wickerwaka/Arcade-IremM92_MiSTer/docs/m92_A-B_B-F/audio.kicad_sch

## KiCad design docs/m92_A-B_B-F/audio.kicad_sch (2023-03-26)

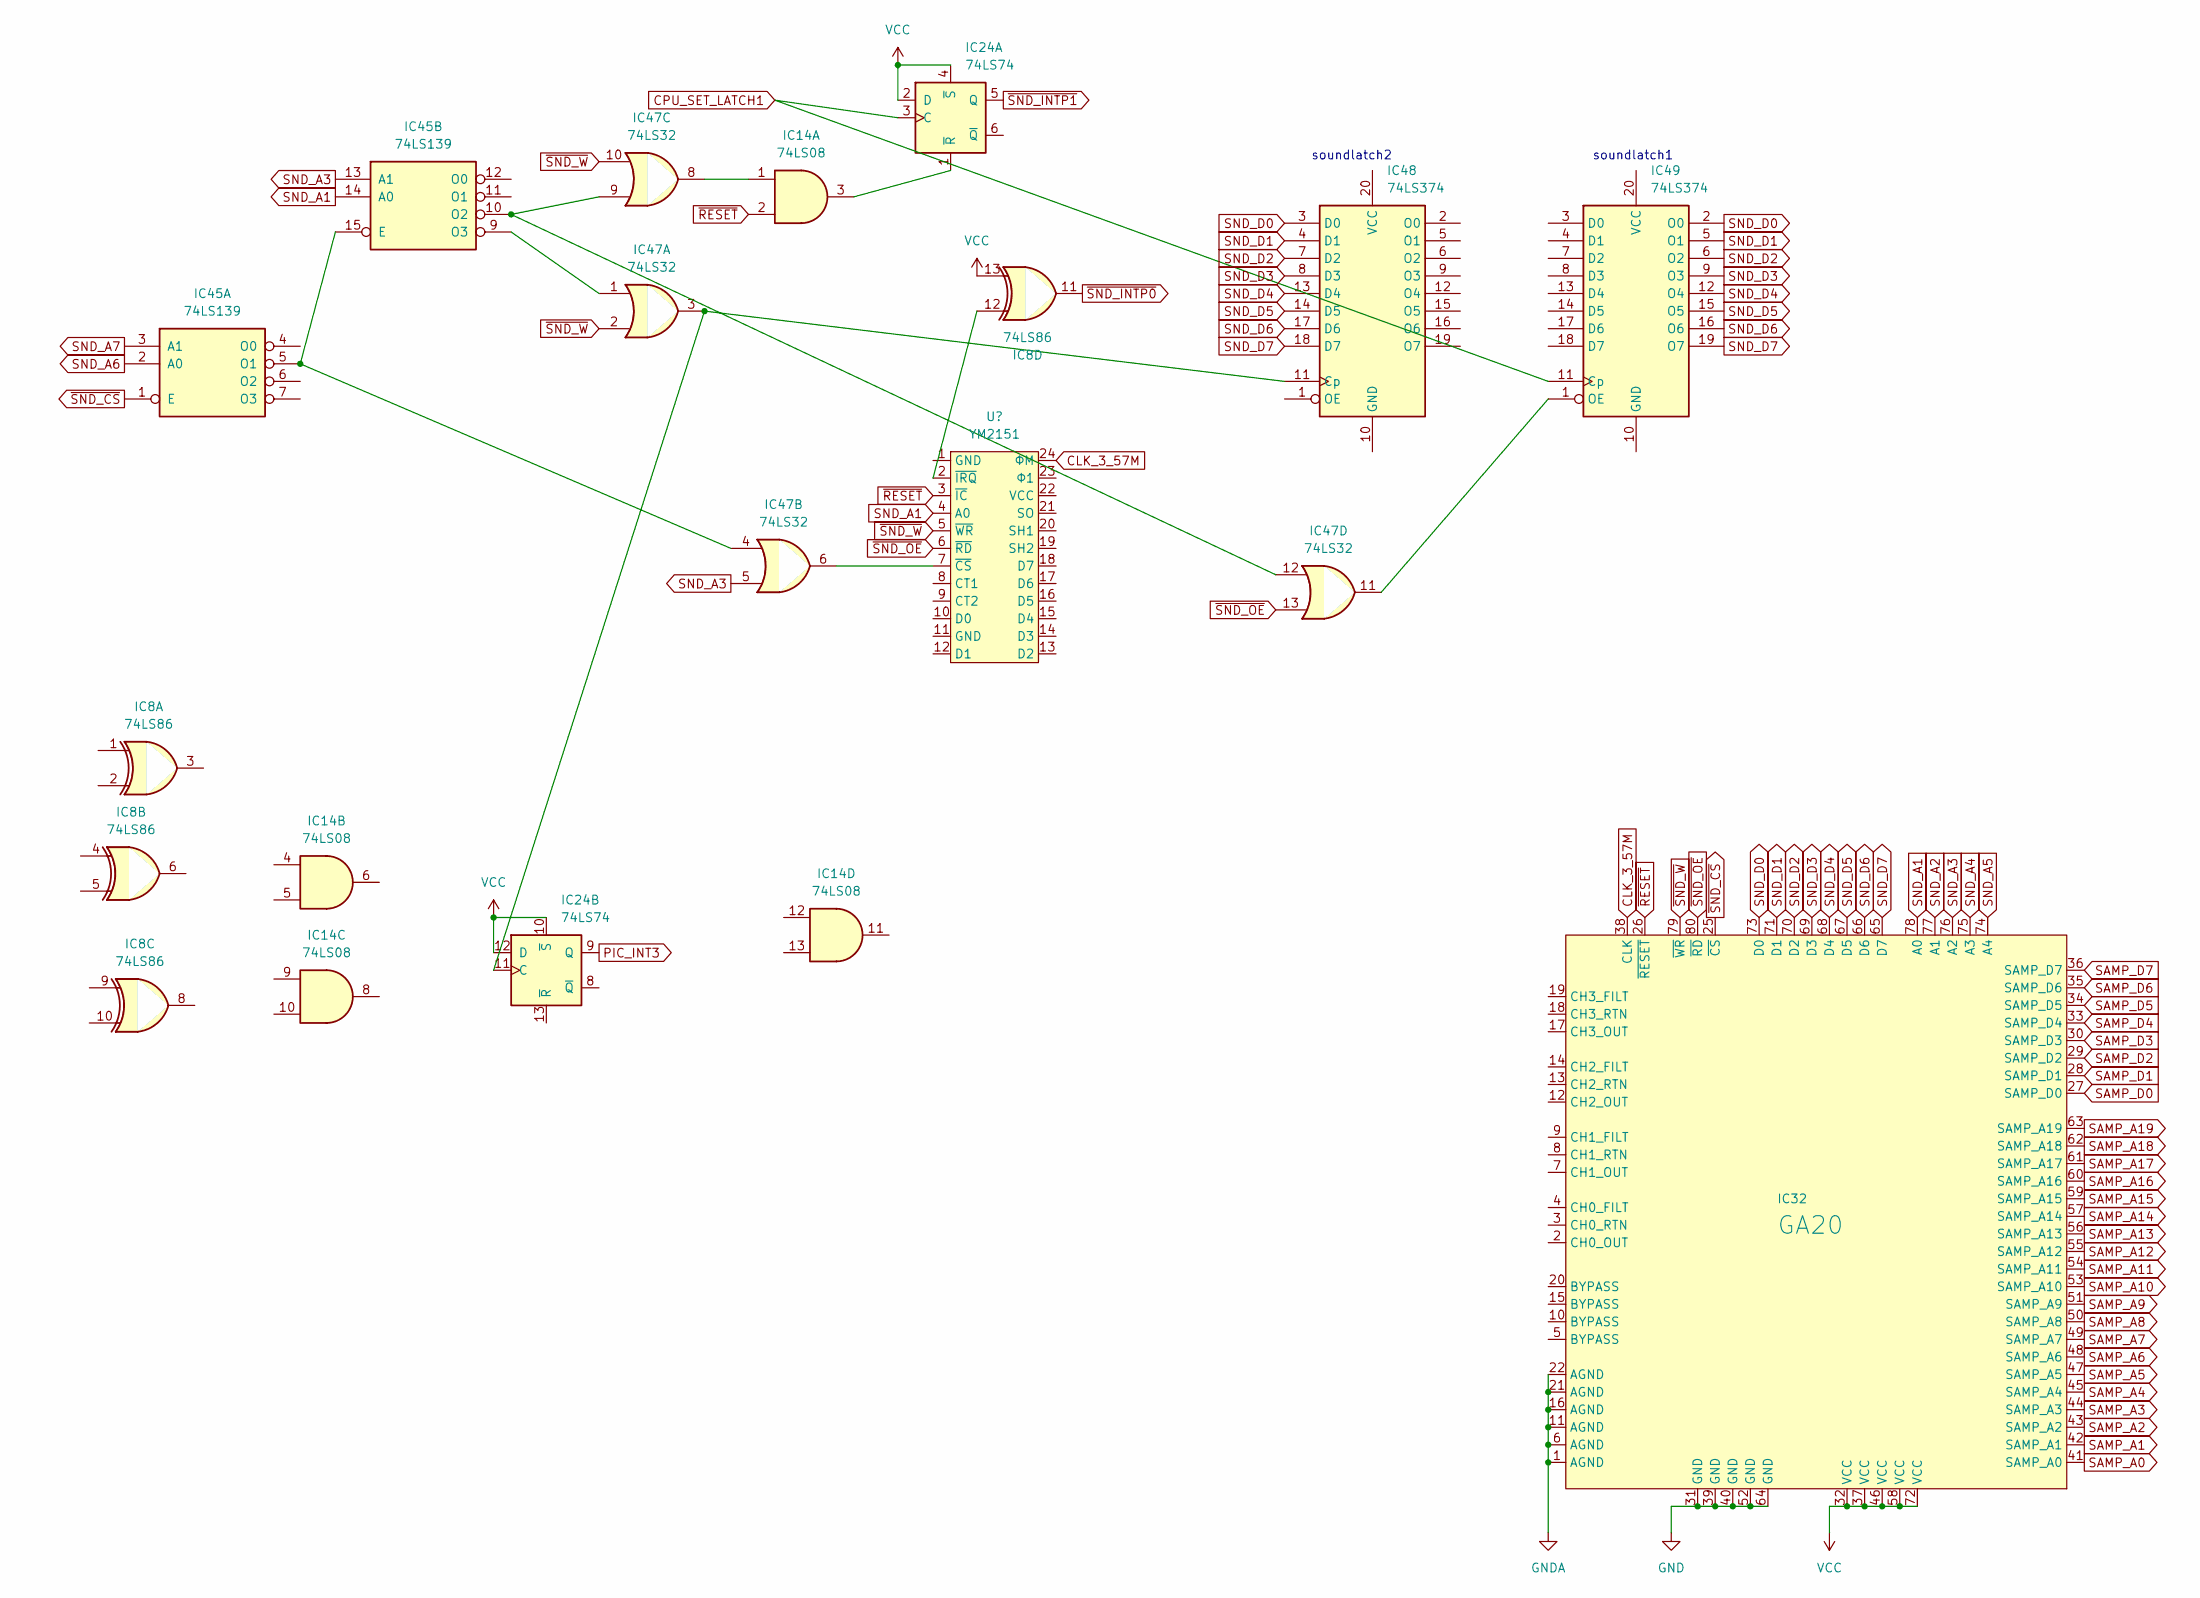
[picture p6: schematic audio.kicad_sch]

Parts:
IC8: 74LS86
IC14: 74LS08
IC24: 74LS74
IC32: GA20
IC45: 74LS139
IC47: 74LS32
IC48, IC49: 74LS374

Connections:
CLK_3_57M: IC32.38 (CLK)
CPU_SET_LATCH1: IC24.3 (C), IC49.11 (Cp)
unnamed: IC14.1, IC47.8
unnamed: IC14.3, IC24.1 (~R)
unnamed: IC24.2 (D), IC24.4 (~S)
unnamed: IC24.10 (~S), IC24.12 (D)
unnamed: IC24.11 (C), IC47.3, IC48.11 (Cp)
unnamed: IC32.1 (AGND), IC32.6 (AGND), IC32.11 (AGND), IC32.16 (AGND), IC32.21 (AGND), IC32.22 (AGND)
unnamed: IC32.31 (GND), IC32.39 (GND), IC32.40 (GND), IC32.52 (GND), IC32.64 (GND)
unnamed: IC32.32 (VCC), IC32.37 (VCC), IC32.46 (VCC), IC32.58 (VCC), IC32.72 (VCC)
unnamed: IC45.9 (O3), IC47.1
unnamed: IC45.10 (O2), IC47.9, IC47.12
unnamed: IC45.5 (O1), IC45.15 (E), IC47.4
unnamed: IC47.11, IC49.1 (OE)
PIC_INT3: IC24.9 (Q)
SAMP_A0: IC32.41 (SAMP_A0)
SAMP_A1: IC32.42 (SAMP_A1)
SAMP_A2: IC32.43 (SAMP_A2)
SAMP_A3: IC32.44 (SAMP_A3)
SAMP_A4: IC32.45 (SAMP_A4)
SAMP_A5: IC32.47 (SAMP_A5)
SAMP_A6: IC32.48 (SAMP_A6)
SAMP_A7: IC32.49 (SAMP_A7)
SAMP_A8: IC32.50 (SAMP_A8)
SAMP_A9: IC32.51 (SAMP_A9)
SAMP_A10: IC32.53 (SAMP_A10)
SAMP_A11: IC32.54 (SAMP_A11)
SAMP_A12: IC32.55 (SAMP_A12)
SAMP_A13: IC32.56 (SAMP_A13)
SAMP_A14: IC32.57 (SAMP_A14)
SAMP_A15: IC32.59 (SAMP_A15)
SAMP_A16: IC32.60 (SAMP_A16)
SAMP_A17: IC32.61 (SAMP_A17)
SAMP_A18: IC32.62 (SAMP_A18)
SAMP_A19: IC32.63 (SAMP_A19)
SAMP_D0: IC32.27 (SAMP_D0)
SAMP_D1: IC32.28 (SAMP_D1)
SAMP_D2: IC32.29 (SAMP_D2)
SAMP_D3: IC32.30 (SAMP_D3)
SAMP_D4: IC32.33 (SAMP_D4)
SAMP_D5: IC32.34 (SAMP_D5)
SAMP_D6: IC32.35 (SAMP_D6)
SAMP_D7: IC32.36 (SAMP_D7)
SND_A1: IC32.78 (A0), IC45.14 (A0)
SND_A2: IC32.77 (A1)
SND_A3: IC32.76 (A2), IC45.13 (A1), IC47.5
SND_A4: IC32.75 (A3)
SND_A5: IC32.74 (A4)
SND_A6: IC45.2 (A0)
SND_A7: IC45.3 (A1)
SND_D0: IC32.73 (D0), IC48.3 (D0), IC49.2 (O0)
SND_D1: IC32.71 (D1), IC48.4 (D1), IC49.5 (O1)
SND_D2: IC32.70 (D2), IC48.7 (D2), IC49.6 (O2)
SND_D3: IC32.69 (D3), IC48.8 (D3), IC49.9 (O3)
SND_D4: IC32.68 (D4), IC48.13 (D4), IC49.12 (O4)
SND_D5: IC32.67 (D5), IC48.14 (D5), IC49.15 (O5)
SND_D6: IC32.66 (D6), IC48.17 (D6), IC49.16 (O6)
SND_D7: IC32.65 (D7), IC48.18 (D7), IC49.19 (O7)
~RESET: IC14.2, IC32.26 (~RESET)
~SND_CS: IC32.25 (~CS), IC45.1 (E)
~SND_INTP0: IC8.11
~SND_INTP1: IC24.5 (Q)
~SND_OE: IC32.80 (~RD), IC47.13
~SND_W: IC32.79 (~WR), IC47.2, IC47.10

Notes on the sheet:
soundlatch2
soundlatch1
