wickerwaka/Arcade-IremM92_MiSTer/docs/m92_A-B_B-F/audio_cpu.kicad_sch

## KiCad design docs/m92_A-B_B-F/audio_cpu.kicad_sch (2023-03-26)

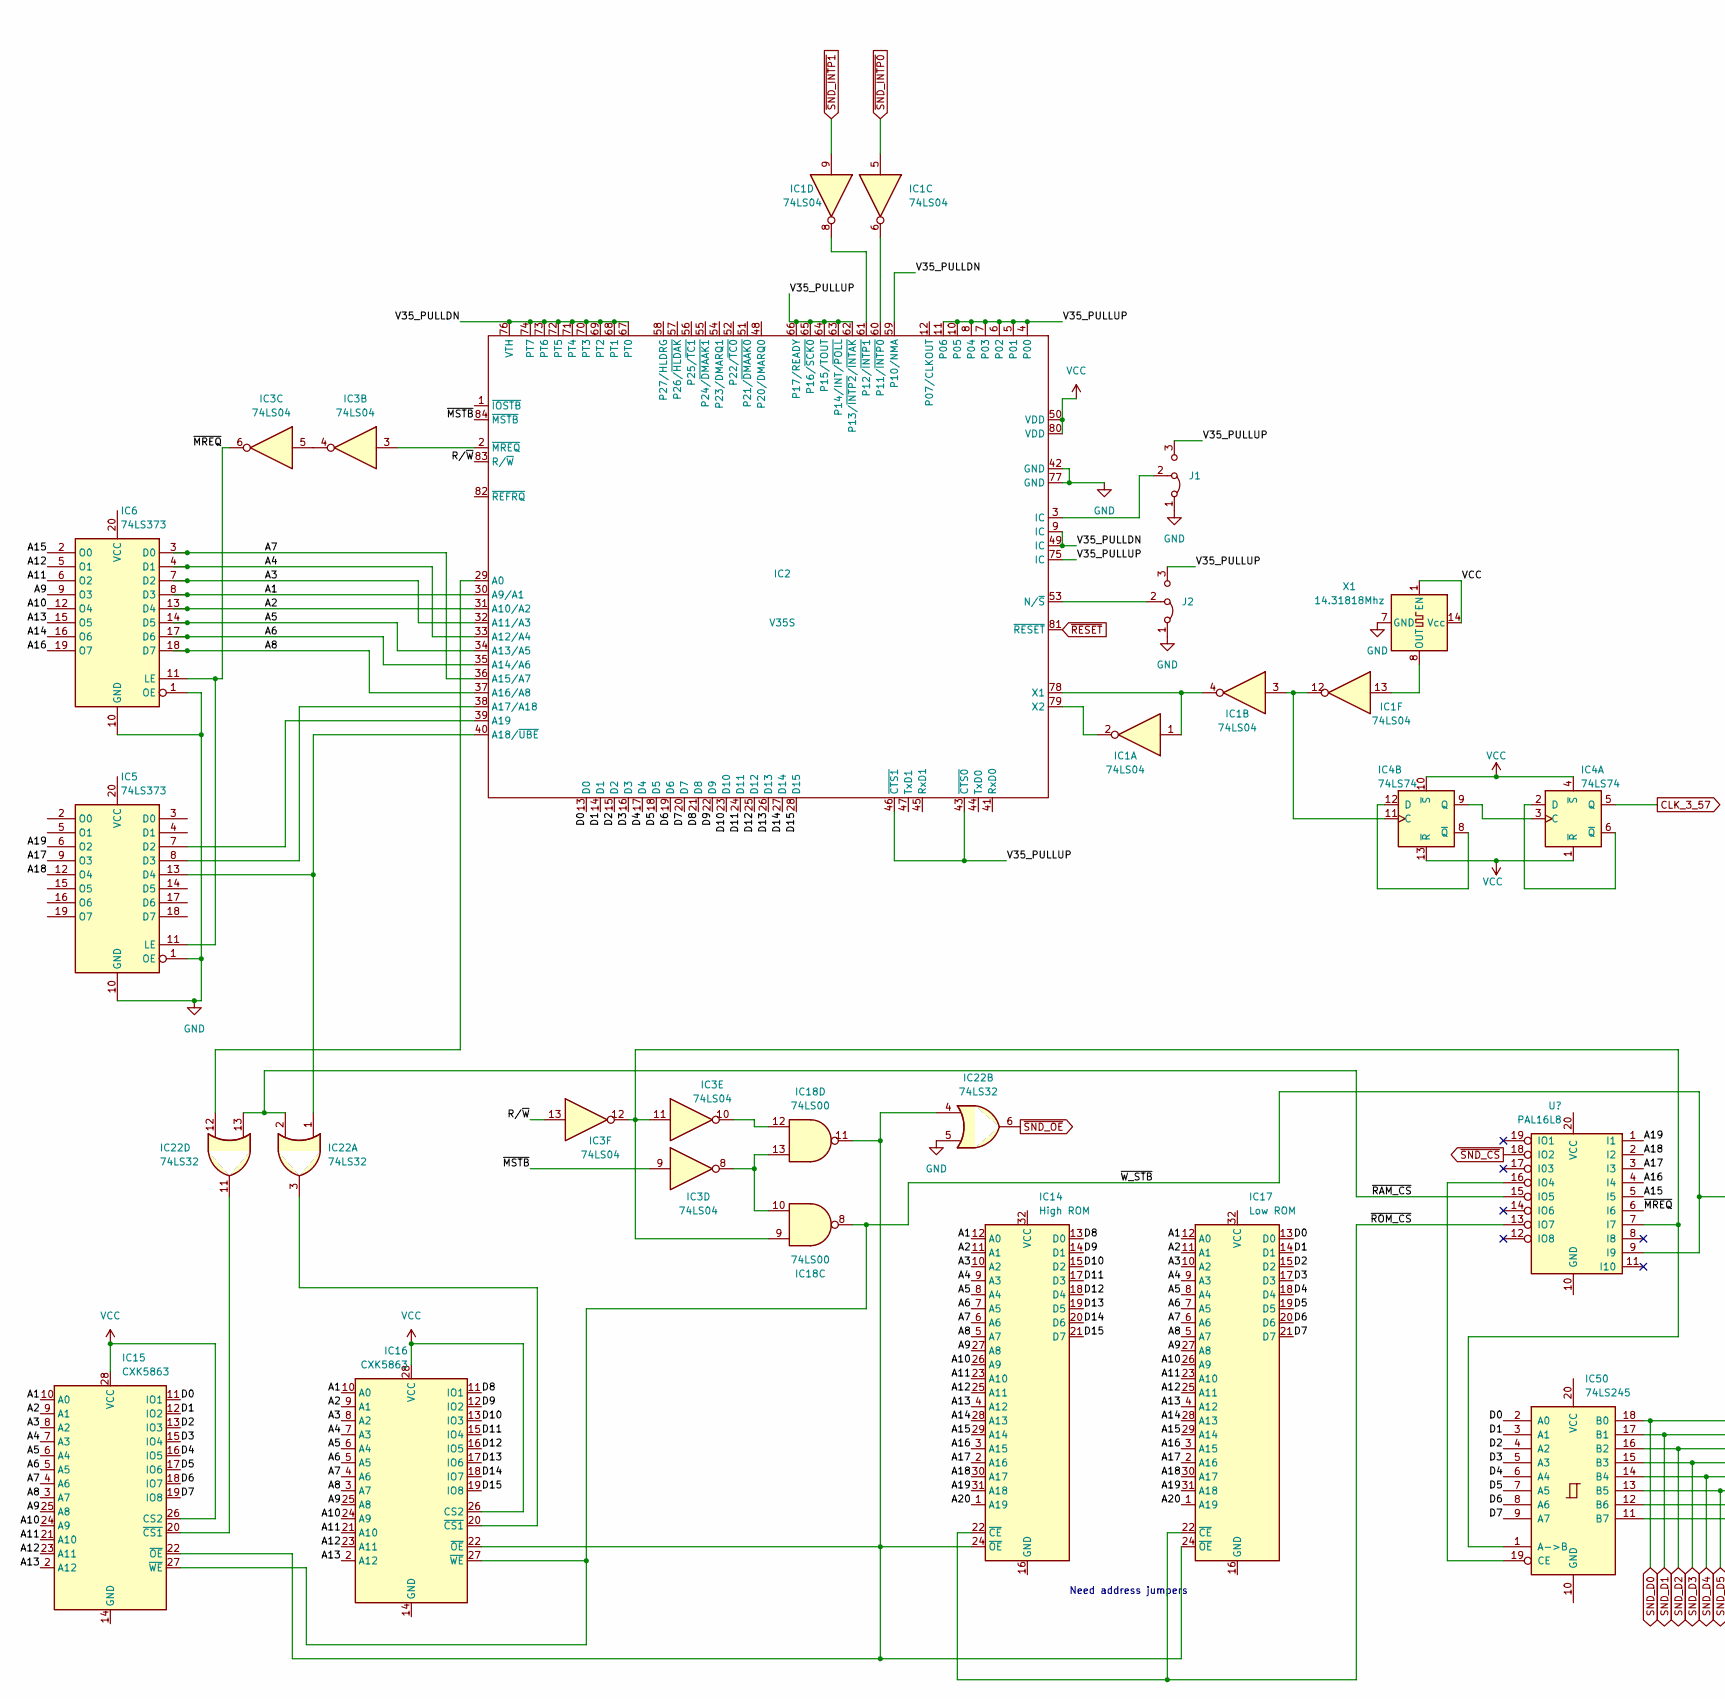
[picture p7: schematic audio_cpu.kicad_sch, part in row 1, column 1]

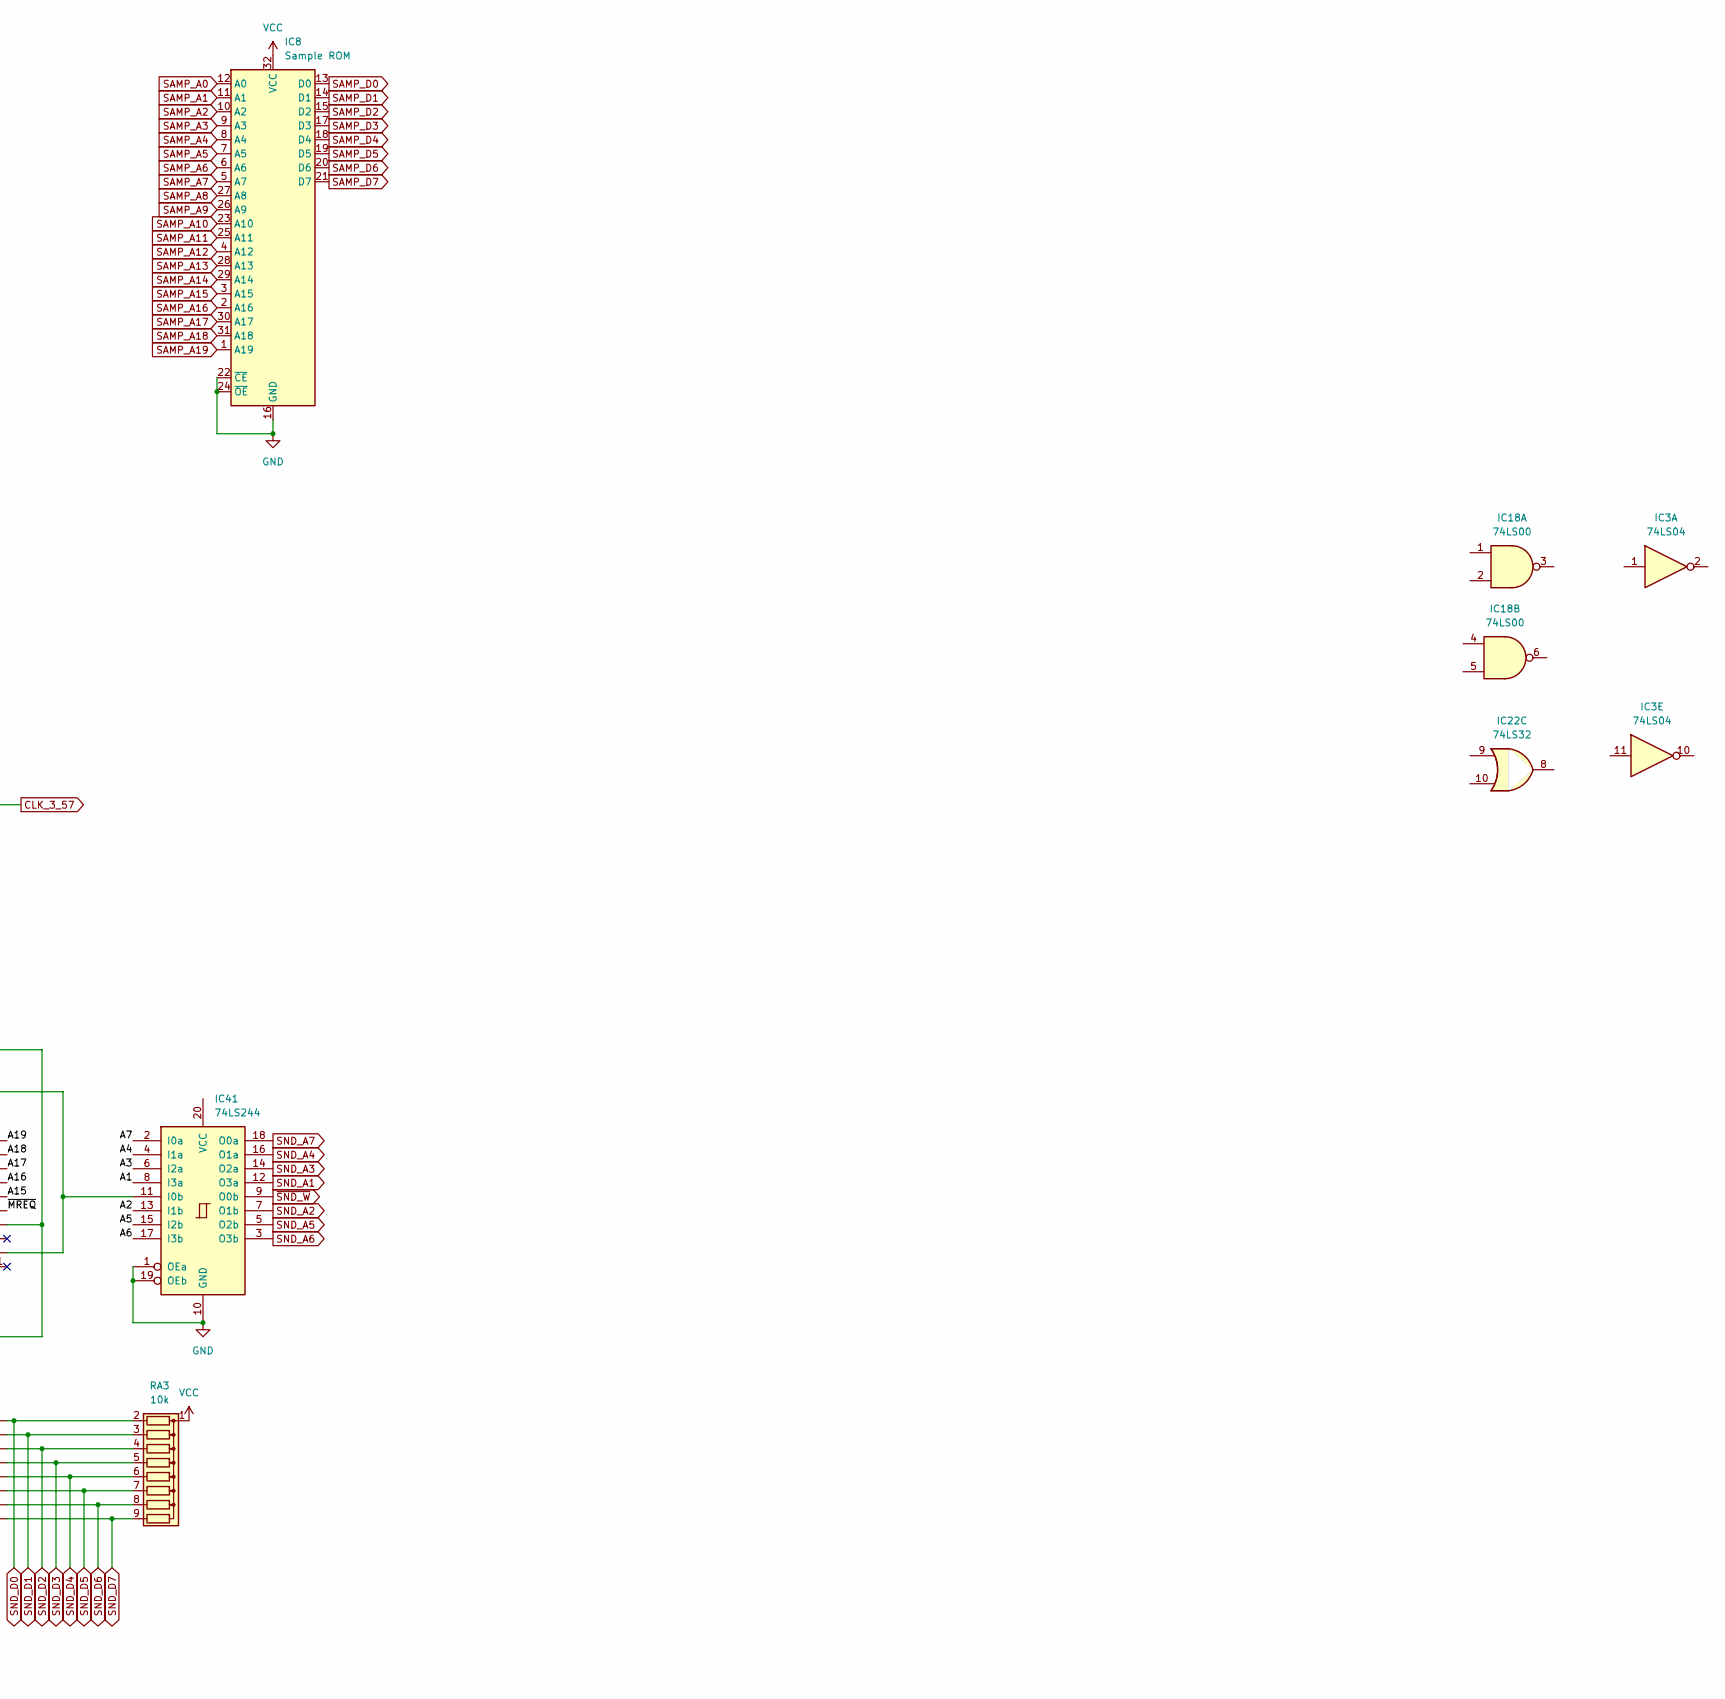
[picture p8: schematic audio_cpu.kicad_sch, part in row 1, column 2]

Parts:
IC1, IC3: 74LS04
IC2: V35S
IC4: 74LS74
IC5, IC6: 74LS373
IC8: Sample ROM
IC14: High ROM
IC15, IC16: CXK5863; DIP-28_W15.24mm
IC17: Low ROM
IC18: 74LS00
IC22: 74LS32
IC41: 74LS244
IC50: 74LS245
J1, J2: Jumper_3_Bridged12
RA3: 10k; R_Array_SIP9
X1: 14.31818Mhz; Oscillator_DIP-14

Connections:
A1: IC2.30 (A9/A1), IC6.8 (D3), IC14.12 (A0), IC15.10 (A0), IC16.10 (A0), IC17.12 (A0), IC41.8 (I3a)
A2: IC2.31 (A10/A2), IC6.13 (D4), IC14.11 (A1), IC15.9 (A1), IC16.9 (A1), IC17.11 (A1), IC41.13 (I1b)
A3: IC2.32 (A11/A3), IC6.7 (D2), IC14.10 (A2), IC15.8 (A2), IC16.8 (A2), IC17.10 (A2), IC41.6 (I2a)
A4: IC2.33 (A12/A4), IC6.4 (D1), IC14.9 (A3), IC15.7 (A3), IC16.7 (A3), IC17.9 (A3), IC41.4 (I1a)
A5: IC2.34 (A13/A5), IC6.14 (D5), IC14.8 (A4), IC15.6 (A4), IC16.6 (A4), IC17.8 (A4), IC41.15 (I2b)
A6: IC2.35 (A14/A6), IC6.17 (D6), IC14.7 (A5), IC15.5 (A5), IC16.5 (A5), IC17.7 (A5), IC41.17 (I3b)
A7: IC2.36 (A15/A7), IC6.3 (D0), IC14.6 (A6), IC15.4 (A6), IC16.4 (A6), IC17.6 (A6), IC41.2 (I0a)
A8: IC2.37 (A16/A8), IC6.18 (D7), IC14.5 (A7), IC15.3 (A7), IC16.3 (A7), IC17.5 (A7)
A9: IC6.9 (O3), IC14.27 (A8), IC15.25 (A8), IC16.25 (A8), IC17.27 (A8)
A10: IC6.12 (O4), IC14.26 (A9), IC15.24 (A9), IC16.24 (A9), IC17.26 (A9)
A11: IC6.6 (O2), IC14.23 (A10), IC15.21 (A10), IC16.21 (A10), IC17.23 (A10)
A12: IC6.5 (O1), IC14.25 (A11), IC15.23 (A11), IC16.23 (A11), IC17.25 (A11)
A13: IC6.15 (O5), IC14.4 (A12), IC15.2 (A12), IC16.2 (A12), IC17.4 (A12)
A14: IC6.16 (O6), IC14.28 (A13), IC17.28 (A13)
A15: IC6.2 (O0), IC14.29 (A14), IC17.29 (A14)
A16: IC6.19 (O7), IC14.3 (A15), IC17.3 (A15)
A17: IC5.9 (O3), IC14.2 (A16), IC17.2 (A16)
A18: IC5.12 (O4), IC14.30 (A17), IC17.30 (A17)
A19: IC5.6 (O2), IC14.31 (A18), IC17.31 (A18)
A20: IC14.1 (A19), IC17.1 (A19)
CLK_3_57: IC4.5 (Q)
D0: IC2.13 (D0), IC15.11 (IO1), IC17.13 (D0), IC50.2 (A0)
D1: IC2.14 (D1), IC15.12 (IO2), IC17.14 (D1), IC50.3 (A1)
D2: IC2.15 (D2), IC15.13 (IO3), IC17.15 (D2), IC50.4 (A2)
D3: IC2.16 (D3), IC15.15 (IO4), IC17.17 (D3), IC50.5 (A3)
D4: IC2.17 (D4), IC15.16 (IO5), IC17.18 (D4), IC50.6 (A4)
D5: IC2.18 (D5), IC15.17 (IO6), IC17.19 (D5), IC50.7 (A5)
D6: IC2.19 (D6), IC15.18 (IO7), IC17.20 (D6), IC50.8 (A6)
D7: IC2.20 (D7), IC15.19 (IO8), IC17.21 (D7), IC50.9 (A7)
D8: IC2.21 (D8), IC14.13 (D0), IC16.11 (IO1)
D9: IC2.22 (D9), IC14.14 (D1), IC16.12 (IO2)
D10: IC2.23 (D10), IC14.15 (D2), IC16.13 (IO3)
D11: IC2.24 (D11), IC14.17 (D3), IC16.15 (IO4)
D12: IC2.25 (D12), IC14.18 (D4), IC16.16 (IO5)
D13: IC2.26 (D13), IC14.19 (D5), IC16.17 (IO6)
D14: IC2.27 (D14), IC14.20 (D6), IC16.18 (IO7)
D15: IC2.28 (D15), IC14.21 (D7), IC16.19 (IO8)
unnamed: IC1.1, IC1.4, IC2.78 (X1)
unnamed: IC1.2, IC2.79 (X2)
unnamed: IC1.6, IC2.60 (P11/~INTP0)
unnamed: IC1.8, IC2.61 (P12/~INTP1)
unnamed: IC1.3, IC1.12, IC4.11 (C)
unnamed: IC1.13, X1.8 (OUT)
unnamed: IC2.2 (~MREQ), IC3.3
unnamed: IC2.3 (IC), J1.2 (C)
unnamed: IC2.29 (A0), IC22.12
unnamed: IC2.38 (A17/A18), IC5.8 (D3)
unnamed: IC2.39 (A19), IC5.7 (D2)
unnamed: IC2.40 (A18/~UBE), IC5.13 (D4), IC22.1
unnamed: IC2.42 (GND), IC2.77 (GND)
unnamed: IC2.50 (VDD), IC2.80 (VDD)
unnamed: IC2.53 (N/~S), J2.2 (C)
unnamed: IC3.4, IC3.5
unnamed: IC4.1 (~R), IC4.13 (~R)
unnamed: IC4.2 (D), IC4.6 (~Q)
unnamed: IC4.3 (C), IC4.9 (Q)
unnamed: IC4.4 (~S), IC4.10 (~S)
unnamed: IC4.8 (~Q), IC4.12 (D)
unnamed: IC5.1 (OE), IC5.10 (GND), IC6.1 (OE), IC6.10 (GND)
unnamed: IC8.16 (GND), IC8.22 (~CE), IC8.24 (~OE)
unnamed: IC14.24 (~OE), IC15.22 (~OE), IC16.22 (~OE), IC17.24 (~OE), IC18.11, IC22.4
unnamed: IC15.20 (~CS1), IC22.11
unnamed: IC15.26 (CS2), IC15.28 (VCC)
unnamed: IC16.20 (~CS1), IC22.3
unnamed: IC16.26 (CS2), IC16.28 (VCC)
unnamed: IC3.11, IC3.12, IC18.9, IC50.1 (A->B)
unnamed: IC3.8, IC18.10, IC18.13
unnamed: IC3.10, IC18.12
unnamed: IC41.1 (OEa), IC41.10 (GND), IC41.19 (OEb)
R/~W: IC2.83 (R/~W), IC3.13
SAMP_A0: IC8.12 (A0)
SAMP_A1: IC8.11 (A1)
SAMP_A2: IC8.10 (A2)
SAMP_A3: IC8.9 (A3)
SAMP_A4: IC8.8 (A4)
SAMP_A5: IC8.7 (A5)
SAMP_A6: IC8.6 (A6)
SAMP_A7: IC8.5 (A7)
SAMP_A8: IC8.27 (A8)
SAMP_A9: IC8.26 (A9)
SAMP_A10: IC8.23 (A10)
SAMP_A11: IC8.25 (A11)
SAMP_A12: IC8.4 (A12)
SAMP_A13: IC8.28 (A13)
SAMP_A14: IC8.29 (A14)
SAMP_A15: IC8.3 (A15)
SAMP_A16: IC8.2 (A16)
SAMP_A17: IC8.30 (A17)
SAMP_A18: IC8.31 (A18)
SAMP_A19: IC8.1 (A19)
SAMP_D0: IC8.13 (D0)
SAMP_D1: IC8.14 (D1)
SAMP_D2: IC8.15 (D2)
SAMP_D3: IC8.17 (D3)
SAMP_D4: IC8.18 (D4)
SAMP_D5: IC8.19 (D5)
SAMP_D6: IC8.20 (D6)
SAMP_D7: IC8.21 (D7)
SND_A1: IC41.12 (O3a)
SND_A2: IC41.7 (O1b)
SND_A3: IC41.14 (O2a)
SND_A4: IC41.16 (O1a)
SND_A5: IC41.5 (O2b)
SND_A6: IC41.3 (O3b)
SND_A7: IC41.18 (O0a)
SND_D0: IC50.18 (B0), RA3.2 (R1)
SND_D1: IC50.17 (B1), RA3.3 (R2)
SND_D2: IC50.16 (B2), RA3.4 (R3)
SND_D3: IC50.15 (B3), RA3.5 (R4)
SND_D4: IC50.14 (B4), RA3.6 (R5)
SND_D5: IC50.13 (B5), RA3.7 (R6)
SND_D6: IC50.12 (B6), RA3.8 (R7)
SND_D7: IC50.11 (B7), RA3.9 (R8)
V35_PULLDN: IC2.9 (IC), IC2.49 (IC), IC2.59 (P10/NMA), IC2.67 (PT0), IC2.68 (PT1), IC2.69 (PT2), IC2.70 (PT3), IC2.71 (PT4), IC2.72 (PT5), IC2.73 (PT6), IC2.74 (PT7), IC2.76 (VTH)
V35_PULLUP: IC2.4 (P00), IC2.5 (P01), IC2.6 (P02), IC2.7 (P03), IC2.8 (P04), IC2.10 (P05), IC2.11 (P06), IC2.43 (~CTS0), IC2.46 (~CTS1), IC2.62 (P13/~INTP2/~INTAK), IC2.63 (P14/INT/~POLL), IC2.64 (P15/TOUT), IC2.65 (P16/~SCK0), IC2.66 (P17/READY), IC2.75 (IC), J1.3 (B), J2.3 (B)
VCC: X1.1 (EN), X1.14 (Vcc)
~MREQ: IC3.6, IC5.11 (LE), IC6.11 (LE)
~MSTB: IC2.84 (~MSTB), IC3.9
~RAM_CS: IC22.2, IC22.13
~RESET: IC2.81 (~RESET)
~ROM_CS: IC14.22 (~CE), IC17.22 (~CE)
~SND_INTP0: IC1.5
~SND_INTP1: IC1.9
~SND_OE: IC22.6
~SND_W: IC41.9 (O0b)
~W_STB: IC15.27 (~WE), IC16.27 (~WE), IC18.8, IC41.11 (I0b)

Notes on the sheet:
Need address jumpers
