wickerwaka/Arcade-IremM92_MiSTer/docs/m92_A-B_B-F/audio_mix.kicad_sch

## KiCad design docs/m92_A-B_B-F/audio_mix.kicad_sch (2023-03-26)

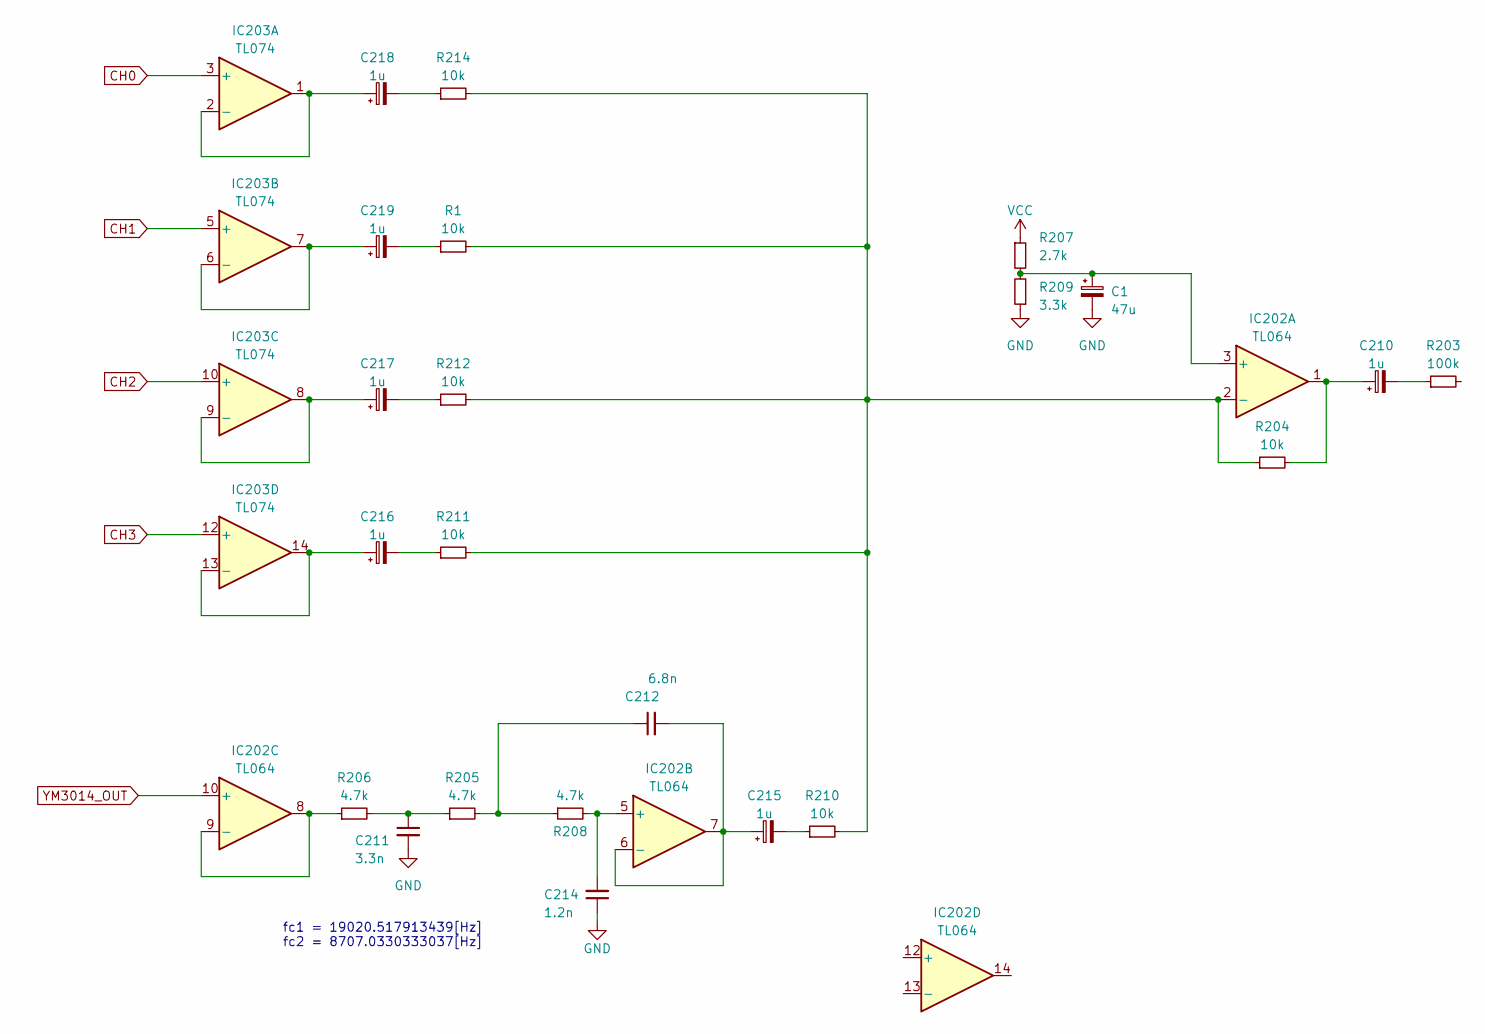
[picture p9: schematic audio_mix.kicad_sch]

Parts:
C1: 47u
C210, C215, C216, C217, C218, C219: 1u
C211: 3.3n
C212: 6.8n
C214: 1.2n
IC202: TL064
IC203: TL074
R1, R204, R210, R211, R212, R214: 10k
R203: 100k
R205, R206, R208: 4.7k
R207: 2.7k
R209: 3.3k

Connections:
CH0: IC203.3 (+)
CH1: IC203.5 (+)
CH2: IC203.10 (+)
CH3: IC203.12 (+)
GND: C1.2, C211.2, C214.1, R209.1
unnamed: C1.1, IC202.3 (+), R207.2, R209.2
unnamed: C210.1, IC202.1, R204.2
unnamed: C210.2, R203.1
unnamed: C211.1, R205.1, R206.2
unnamed: C212.1, R205.2, R208.1
unnamed: C212.2, C215.1, IC202.6 (-), IC202.7
unnamed: C214.2, IC202.5 (+), R208.2
unnamed: C215.2, R210.1
unnamed: C216.1, IC203.13 (-), IC203.14
unnamed: C216.2, R211.1
unnamed: C217.1, IC203.8, IC203.9 (-)
unnamed: C217.2, R212.1
unnamed: C218.1, IC203.1, IC203.2 (-)
unnamed: C218.2, R214.1
unnamed: C219.1, IC203.6 (-), IC203.7
unnamed: C219.2, R1.1
unnamed: IC202.2 (-), R1.2, R204.1, R210.2, R211.2, R212.2, R214.2
unnamed: IC202.8, IC202.9 (-), R206.1
VCC: R207.1
YM3014_OUT: IC202.10 (+)

Notes on the sheet:
fc1 = 19020.517913439[Hz] fc2 = 8707.0330333037[Hz]
