wickerwaka/Arcade-IremM92_MiSTer/docs/m92_A-B_B-F/b_board_support.kicad_sch

## KiCad design docs/m92_A-B_B-F/b_board_support.kicad_sch (2023-03-26)

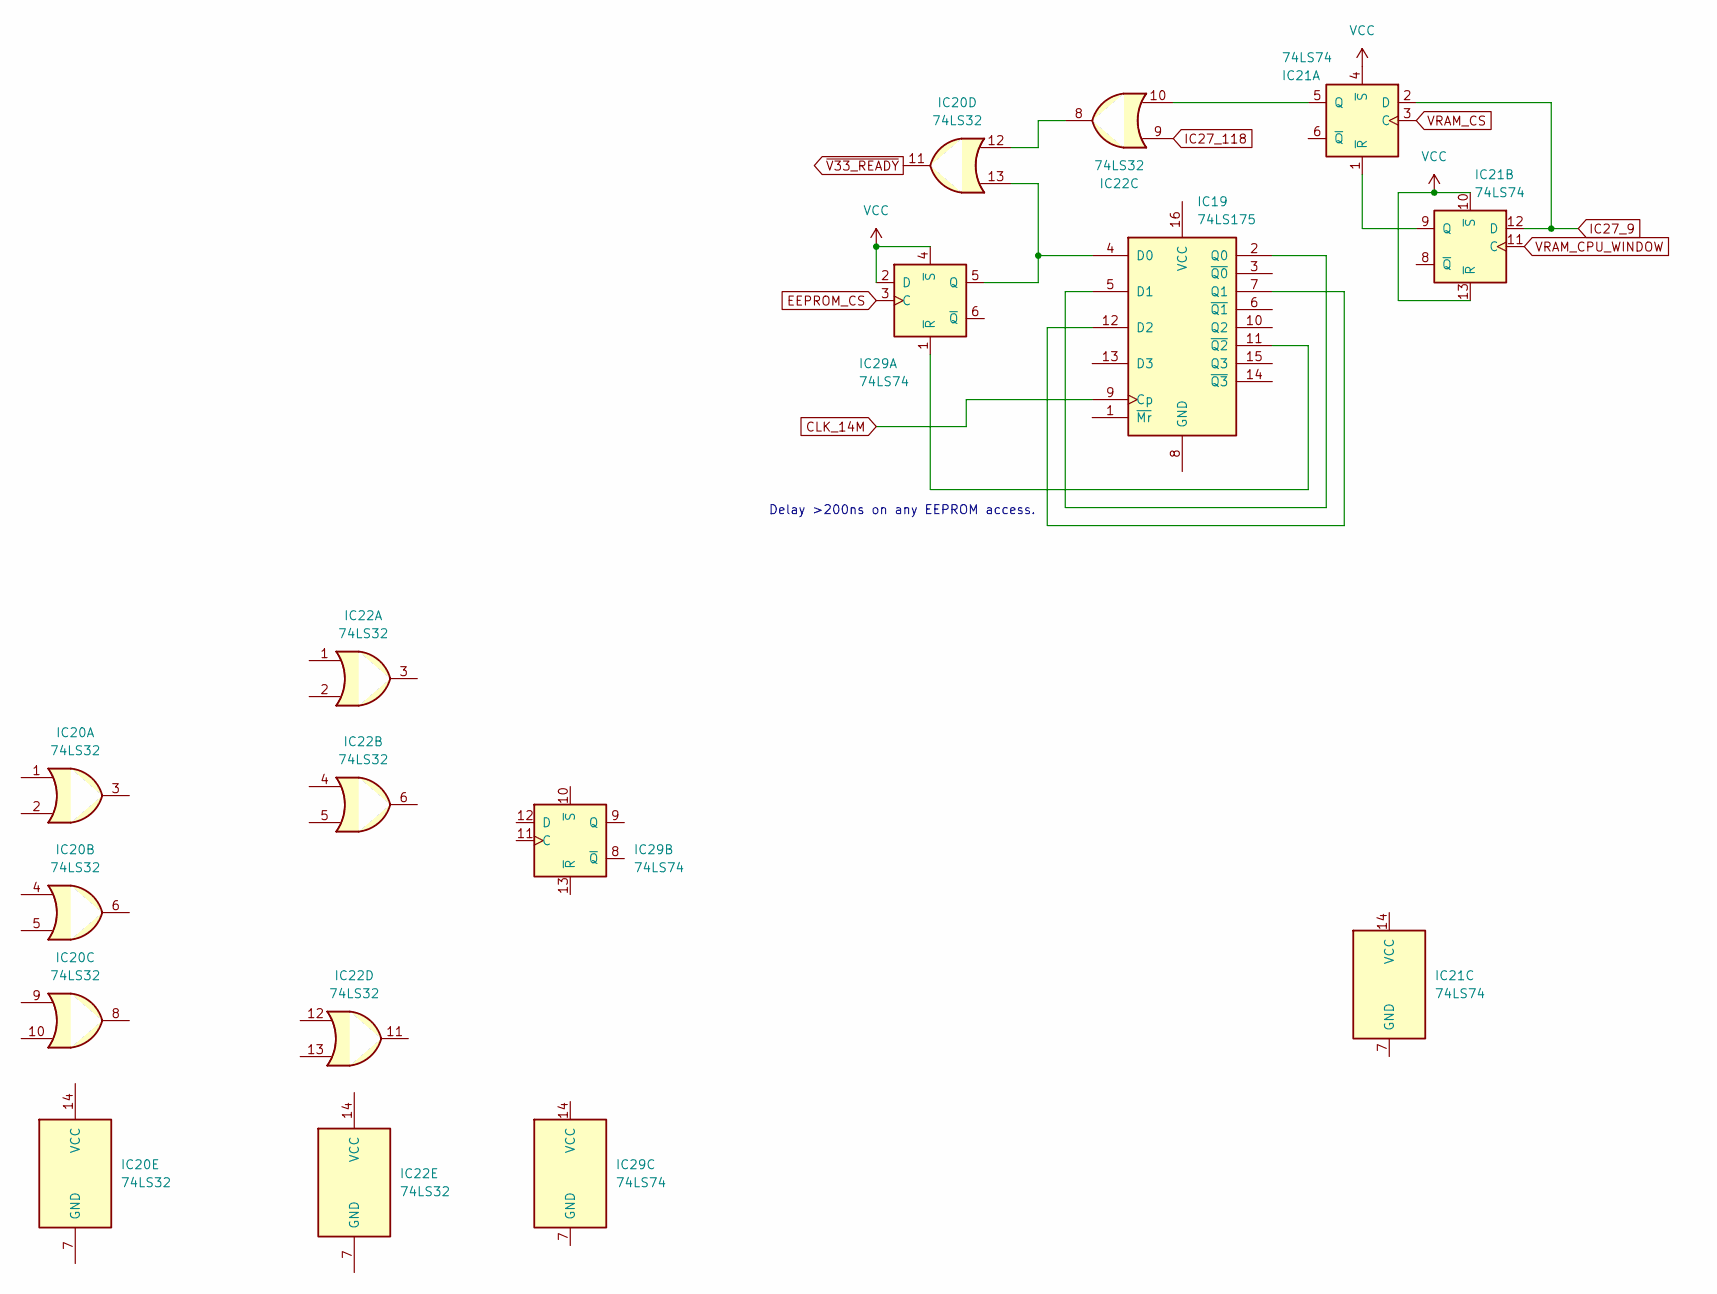
[picture p10: schematic b_board_support.kicad_sch]

Parts:
IC19: 74LS175
IC20, IC22: 74LS32
IC21, IC29: 74LS74

Connections:
CLK_14M: IC19.9 (Cp)
EEPROM_CS: IC29.3 (C)
IC27_9: IC21.2 (D), IC21.12 (D)
IC27_118: IC22.9
unnamed: IC19.2 (Q0), IC19.5 (D1)
unnamed: IC19.4 (D0), IC20.13, IC29.5 (Q)
unnamed: IC19.11 (~Q2), IC29.1 (~R)
unnamed: IC19.7 (Q1), IC19.12 (D2)
unnamed: IC20.12, IC22.8
unnamed: IC21.1 (~R), IC21.9 (Q)
unnamed: IC21.5 (Q), IC22.10
unnamed: IC21.10 (~S), IC21.13 (~R)
unnamed: IC29.2 (D), IC29.4 (~S)
VRAM_CPU_WINDOW: IC21.11 (C)
VRAM_CS: IC21.3 (C)
~V33_READY: IC20.11

Notes on the sheet:
Delay >200ns on any EEPROM access.
