wickerwaka/Arcade-IremM92_MiSTer/docs/m92_A-B_B-F/b_interface.kicad_sch

## KiCad design docs/m92_A-B_B-F/b_interface.kicad_sch (2023-03-26)

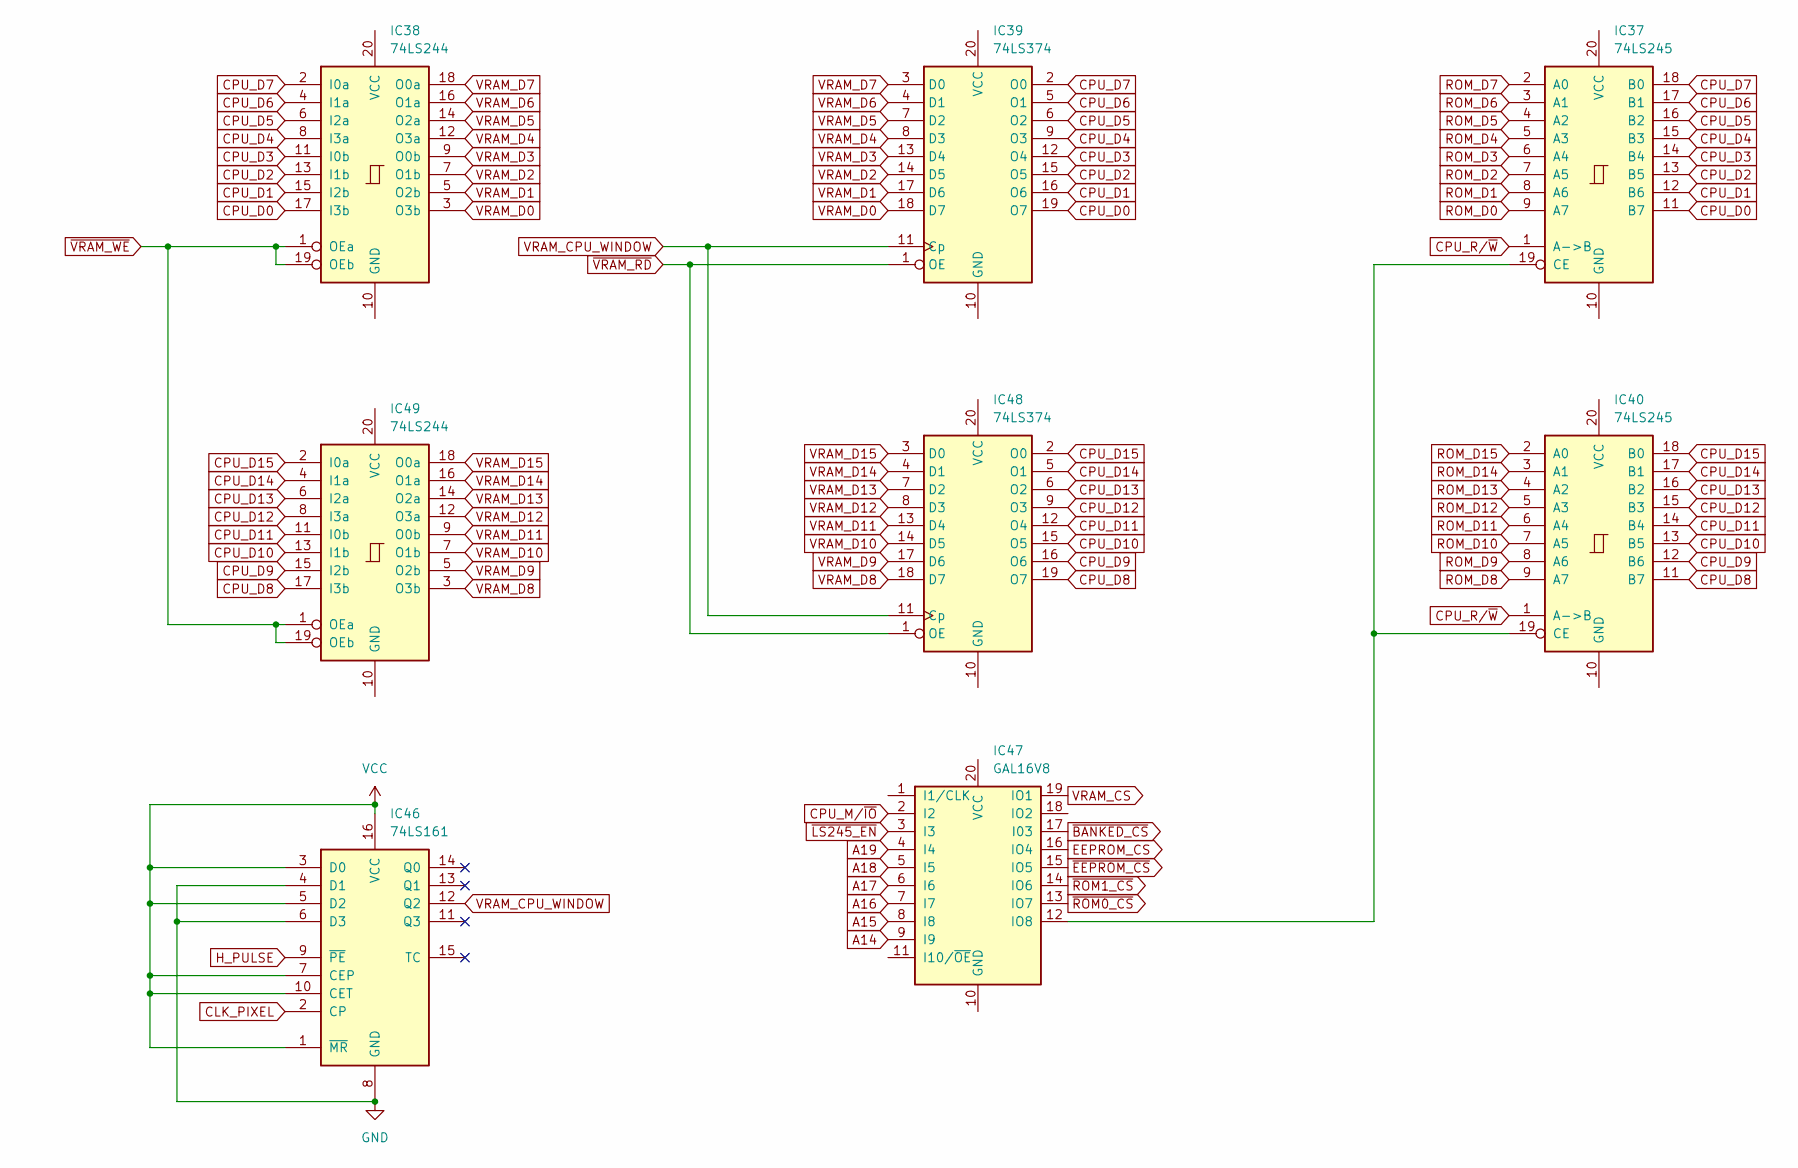
[picture p11: schematic b_interface.kicad_sch]

Parts:
IC37, IC40: 74LS245
IC38, IC49: 74LS244
IC39, IC48: 74LS374
IC46: 74LS161
IC47: GAL16V8

Connections:
A14: IC47.9 (I9)
A15: IC47.8 (I8)
A16: IC47.7 (I7)
A17: IC47.6 (I6)
A18: IC47.5 (I5)
A19: IC47.4 (I4)
CLK_PIXEL: IC46.2 (CP)
CPU_D0: IC37.11 (B7), IC38.17 (I3b), IC39.19 (O7)
CPU_D1: IC37.12 (B6), IC38.15 (I2b), IC39.16 (O6)
CPU_D2: IC37.13 (B5), IC38.13 (I1b), IC39.15 (O5)
CPU_D3: IC37.14 (B4), IC38.11 (I0b), IC39.12 (O4)
CPU_D4: IC37.15 (B3), IC38.8 (I3a), IC39.9 (O3)
CPU_D5: IC37.16 (B2), IC38.6 (I2a), IC39.6 (O2)
CPU_D6: IC37.17 (B1), IC38.4 (I1a), IC39.5 (O1)
CPU_D7: IC37.18 (B0), IC38.2 (I0a), IC39.2 (O0)
CPU_D8: IC40.11 (B7), IC48.19 (O7), IC49.17 (I3b)
CPU_D9: IC40.12 (B6), IC48.16 (O6), IC49.15 (I2b)
CPU_D10: IC40.13 (B5), IC48.15 (O5), IC49.13 (I1b)
CPU_D11: IC40.14 (B4), IC48.12 (O4), IC49.11 (I0b)
CPU_D12: IC40.15 (B3), IC48.9 (O3), IC49.8 (I3a)
CPU_D13: IC40.16 (B2), IC48.6 (O2), IC49.6 (I2a)
CPU_D14: IC40.17 (B1), IC48.5 (O1), IC49.4 (I1a)
CPU_D15: IC40.18 (B0), IC48.2 (O0), IC49.2 (I0a)
CPU_M/~IO: IC47.2 (I2)
CPU_R/~W: IC37.1 (A->B), IC40.1 (A->B)
EEPROM_CS: IC47.16 (IO4)
H_PULSE: IC46.9 (~PE)
unnamed: IC37.19 (CE), IC40.19 (CE), IC47.12 (IO8)
unnamed: IC46.1 (~MR), IC46.3 (D0), IC46.5 (D2), IC46.7 (CEP), IC46.10 (CET), IC46.16 (VCC)
unnamed: IC46.4 (D1), IC46.6 (D3), IC46.8 (GND)
ROM_D0: IC37.9 (A7)
ROM_D1: IC37.8 (A6)
ROM_D2: IC37.7 (A5)
ROM_D3: IC37.6 (A4)
ROM_D4: IC37.5 (A3)
ROM_D5: IC37.4 (A2)
ROM_D6: IC37.3 (A1)
ROM_D7: IC37.2 (A0)
ROM_D8: IC40.9 (A7)
ROM_D9: IC40.8 (A6)
ROM_D10: IC40.7 (A5)
ROM_D11: IC40.6 (A4)
ROM_D12: IC40.5 (A3)
ROM_D13: IC40.4 (A2)
ROM_D14: IC40.3 (A1)
ROM_D15: IC40.2 (A0)
VRAM_CPU_WINDOW: IC39.11 (Cp), IC46.12 (Q2), IC48.11 (Cp)
VRAM_CS: IC47.19 (IO1)
VRAM_D0: IC38.3 (O3b), IC39.18 (D7)
VRAM_D1: IC38.5 (O2b), IC39.17 (D6)
VRAM_D2: IC38.7 (O1b), IC39.14 (D5)
VRAM_D3: IC38.9 (O0b), IC39.13 (D4)
VRAM_D4: IC38.12 (O3a), IC39.8 (D3)
VRAM_D5: IC38.14 (O2a), IC39.7 (D2)
VRAM_D6: IC38.16 (O1a), IC39.4 (D1)
VRAM_D7: IC38.18 (O0a), IC39.3 (D0)
VRAM_D8: IC48.18 (D7), IC49.3 (O3b)
VRAM_D9: IC48.17 (D6), IC49.5 (O2b)
VRAM_D10: IC48.14 (D5), IC49.7 (O1b)
VRAM_D11: IC48.13 (D4), IC49.9 (O0b)
VRAM_D12: IC48.8 (D3), IC49.12 (O3a)
VRAM_D13: IC48.7 (D2), IC49.14 (O2a)
VRAM_D14: IC48.4 (D1), IC49.16 (O1a)
VRAM_D15: IC48.3 (D0), IC49.18 (O0a)
~BANKED_CS: IC47.17 (I03)
~EEPROM_CS: IC47.15 (IO5)
~LS245_EN: IC47.3 (I3)
~ROM0_CS: IC47.13 (IO7)
~ROM1_CS: IC47.14 (IO6)
~VRAM_RD: IC39.1 (OE), IC48.1 (OE)
~VRAM_WE: IC38.1 (OEa), IC38.19 (OEb), IC49.1 (OEa), IC49.19 (OEb)
