wickerwaka/Arcade-IremM92_MiSTer/docs/m92_A-B_B-F/bank_switching.kicad_sch

## KiCad design docs/m92_A-B_B-F/bank_switching.kicad_sch (2023-03-26)

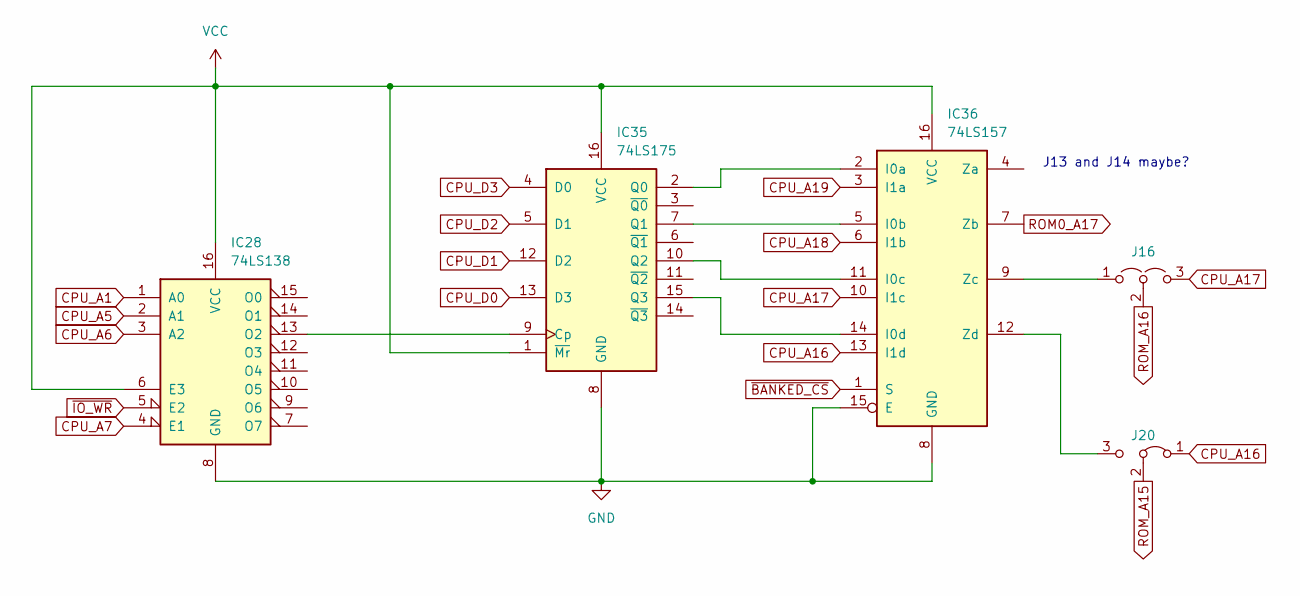
[picture p12: schematic bank_switching.kicad_sch]

Parts:
IC28: 74LS138
IC35: 74LS175
IC36: 74LS157
J16: Jumper_3_Open
J20: Jumper_3_Bridged12

Connections:
CPU_A1: IC28.1 (A0)
CPU_A5: IC28.2 (A1)
CPU_A6: IC28.3 (A2)
CPU_A7: IC28.4 (E1)
CPU_A16: IC36.13 (I1d), J20.1 (A)
CPU_A17: IC36.10 (I1c), J16.3 (B)
CPU_A18: IC36.6 (I1b)
CPU_A19: IC36.3 (I1a)
CPU_D0: IC35.13 (D3)
CPU_D1: IC35.12 (D2)
CPU_D2: IC35.5 (D1)
CPU_D3: IC35.4 (D0)
unnamed: IC28.8 (GND), IC35.8 (GND), IC36.8 (GND), IC36.15 (E)
unnamed: IC28.13 (O2), IC35.9 (Cp)
unnamed: IC28.6 (E3), IC28.16 (VCC), IC35.1 (~Mr), IC35.16 (VCC), IC36.16 (VCC)
unnamed: IC35.2 (Q0), IC36.2 (I0a)
unnamed: IC35.7 (Q1), IC36.5 (I0b)
unnamed: IC35.10 (Q2), IC36.11 (I0c)
unnamed: IC35.15 (Q3), IC36.14 (I0d)
unnamed: IC36.9 (Zc), J16.1 (A)
unnamed: IC36.12 (Zd), J20.3 (B)
ROM0_A17: IC36.7 (Zb)
ROM_A15: J20.2 (C)
ROM_A16: J16.2 (C)
~BANKED_CS: IC36.1 (S)
~IO_WR: IC28.5 (E2)

Notes on the sheet:
J13 and J14 maybe?
