wickerwaka/Arcade-IremM92_MiSTer/docs/m92_A-B_B-F/clock_gen.kicad_sch

## KiCad design docs/m92_A-B_B-F/clock_gen.kicad_sch (2023-03-26)

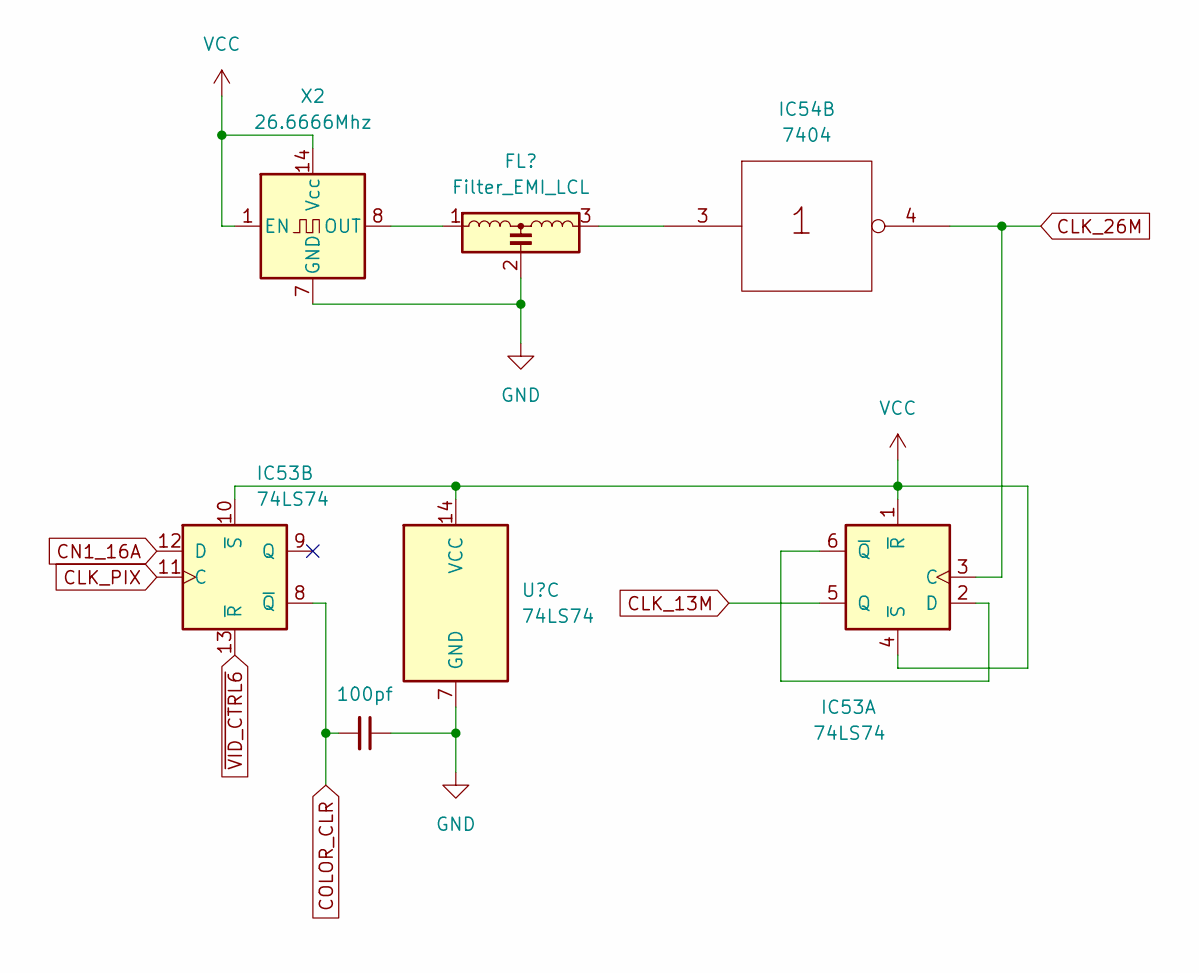
[picture p13: schematic clock_gen.kicad_sch]

Parts:
IC53: 74LS74
IC54: 7404
X2: 26.6666Mhz; Oscillator_DIP-14

Connections:
CLK_13M: IC53.5 (Q)
CLK_26M: IC53.3 (C), IC54.4
CLK_PIX: IC53.11 (C)
CN1_16A: IC53.12 (D)
COLOR_CLR: IC53.8 (~Q)
unnamed: IC53.1 (~R), IC53.4 (~S), IC53.10 (~S)
unnamed: IC53.2 (D), IC53.6 (~Q)
unnamed: X2.1 (EN), X2.14 (Vcc)
~VID_CTRL6: IC53.13 (~R)
