wickerwaka/Arcade-IremM92_MiSTer/docs/m92_A-B_B-F/connectors.kicad_sch

## KiCad design docs/m92_A-B_B-F/connectors.kicad_sch (2023-03-26)

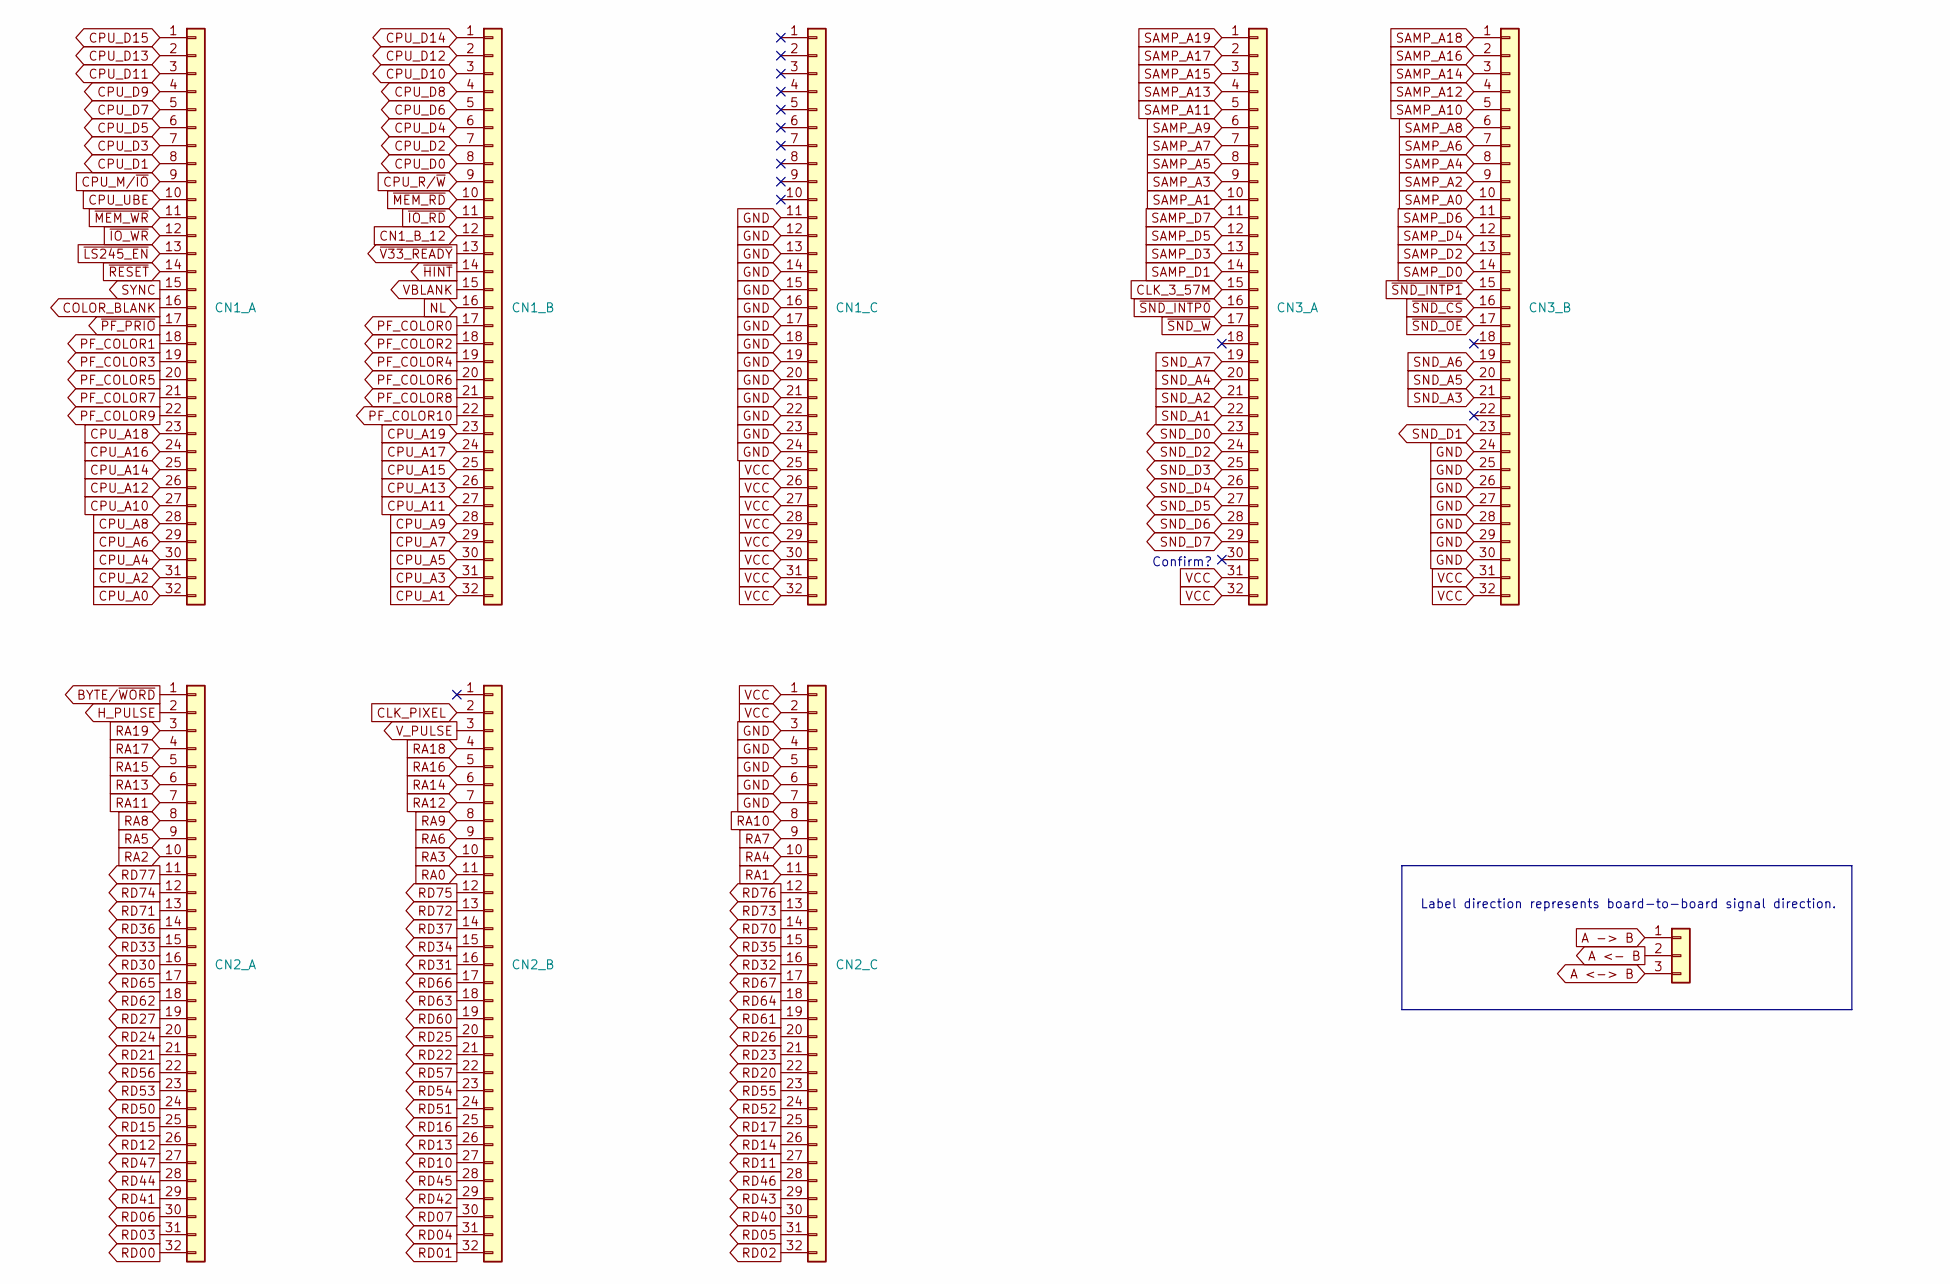
[picture p14: schematic connectors.kicad_sch]

Parts:
CN1_A, CN1_B, CN1_C, CN2_A, CN2_B, CN2_C, CN3_A, CN3_B: Conn_01x32

Connections:
BYTE/~WORD: CN2_A.1
CLK_3_57M: CN3_A.15
CLK_PIXEL: CN2_B.2
CN1_B_12: CN1_B.12
COLOR_BLANK: CN1_A.16
CPU_A0: CN1_A.32
CPU_A1: CN1_B.32
CPU_A2: CN1_A.31
CPU_A3: CN1_B.31
CPU_A4: CN1_A.30
CPU_A5: CN1_B.30
CPU_A6: CN1_A.29
CPU_A7: CN1_B.29
CPU_A8: CN1_A.28
CPU_A9: CN1_B.28
CPU_A10: CN1_A.27
CPU_A11: CN1_B.27
CPU_A12: CN1_A.26
CPU_A13: CN1_B.26
CPU_A14: CN1_A.25
CPU_A15: CN1_B.25
CPU_A16: CN1_A.24
CPU_A17: CN1_B.24
CPU_A18: CN1_A.23
CPU_A19: CN1_B.23
CPU_D0: CN1_B.8
CPU_D1: CN1_A.8
CPU_D2: CN1_B.7
CPU_D3: CN1_A.7
CPU_D4: CN1_B.6
CPU_D5: CN1_A.6
CPU_D6: CN1_B.5
CPU_D7: CN1_A.5
CPU_D8: CN1_B.4
CPU_D9: CN1_A.4
CPU_D10: CN1_B.3
CPU_D11: CN1_A.3
CPU_D12: CN1_B.2
CPU_D13: CN1_A.2
CPU_D14: CN1_B.1
CPU_D15: CN1_A.1
CPU_M/~IO: CN1_A.9
CPU_R/~W: CN1_B.9
CPU_UBE: CN1_A.10
GND: CN1_C.11, CN1_C.12, CN1_C.13, CN1_C.14, CN1_C.15, CN1_C.16, CN1_C.17, CN1_C.18, CN1_C.19, CN1_C.20, CN1_C.21, CN1_C.22, CN1_C.23, CN1_C.24, CN2_C.3, CN2_C.4, CN2_C.5, CN2_C.6, CN2_C.7, CN3_B.24, CN3_B.25, CN3_B.26, CN3_B.27, CN3_B.28, CN3_B.29, CN3_B.30
H_PULSE: CN2_A.2
NL: CN1_B.16
PF_COLOR0: CN1_B.17
PF_COLOR1: CN1_A.18
PF_COLOR2: CN1_B.18
PF_COLOR3: CN1_A.19
PF_COLOR4: CN1_B.19
PF_COLOR5: CN1_A.20
PF_COLOR6: CN1_B.20
PF_COLOR7: CN1_A.21
PF_COLOR8: CN1_B.21
PF_COLOR9: CN1_A.22
PF_COLOR10: CN1_B.22
RA0: CN2_B.11
RA1: CN2_C.11
RA2: CN2_A.10
RA3: CN2_B.10
RA4: CN2_C.10
RA5: CN2_A.9
RA6: CN2_B.9
RA7: CN2_C.9
RA8: CN2_A.8
RA9: CN2_B.8
RA10: CN2_C.8
RA11: CN2_A.7
RA12: CN2_B.7
RA13: CN2_A.6
RA14: CN2_B.6
RA15: CN2_A.5
RA16: CN2_B.5
RA17: CN2_A.4
RA18: CN2_B.4
RA19: CN2_A.3
RD00: CN2_A.32
RD01: CN2_B.32
RD02: CN2_C.32
RD03: CN2_A.31
RD04: CN2_B.31
RD05: CN2_C.31
RD06: CN2_A.30
RD07: CN2_B.30
RD10: CN2_B.27
RD11: CN2_C.27
RD12: CN2_A.26
RD13: CN2_B.26
RD14: CN2_C.26
RD15: CN2_A.25
RD16: CN2_B.25
RD17: CN2_C.25
RD20: CN2_C.22
RD21: CN2_A.21
RD22: CN2_B.21
RD23: CN2_C.21
RD24: CN2_A.20
RD25: CN2_B.20
RD26: CN2_C.20
RD27: CN2_A.19
RD30: CN2_A.16
RD31: CN2_B.16
RD32: CN2_C.16
RD33: CN2_A.15
RD34: CN2_B.15
RD35: CN2_C.15
RD36: CN2_A.14
RD37: CN2_B.14
RD40: CN2_C.30
RD41: CN2_A.29
RD42: CN2_B.29
RD43: CN2_C.29
RD44: CN2_A.28
RD45: CN2_B.28
RD46: CN2_C.28
RD47: CN2_A.27
RD50: CN2_A.24
RD51: CN2_B.24
RD52: CN2_C.24
RD53: CN2_A.23
RD54: CN2_B.23
RD55: CN2_C.23
RD56: CN2_A.22
RD57: CN2_B.22
RD60: CN2_B.19
RD61: CN2_C.19
RD62: CN2_A.18
RD63: CN2_B.18
RD64: CN2_C.18
RD65: CN2_A.17
RD66: CN2_B.17
RD67: CN2_C.17
RD70: CN2_C.14
RD71: CN2_A.13
RD72: CN2_B.13
RD73: CN2_C.13
RD74: CN2_A.12
RD75: CN2_B.12
RD76: CN2_C.12
RD77: CN2_A.11
SAMP_A0: CN3_B.10
SAMP_A1: CN3_A.10
SAMP_A2: CN3_B.9
SAMP_A3: CN3_A.9
SAMP_A4: CN3_B.8
SAMP_A5: CN3_A.8
SAMP_A6: CN3_B.7
SAMP_A7: CN3_A.7
SAMP_A8: CN3_B.6
SAMP_A9: CN3_A.6
SAMP_A10: CN3_B.5
SAMP_A11: CN3_A.5
SAMP_A12: CN3_B.4
SAMP_A13: CN3_A.4
SAMP_A14: CN3_B.3
SAMP_A15: CN3_A.3
SAMP_A16: CN3_B.2
SAMP_A17: CN3_A.2
SAMP_A18: CN3_B.1
SAMP_A19: CN3_A.1
SAMP_D0: CN3_B.14
SAMP_D1: CN3_A.14
SAMP_D2: CN3_B.13
SAMP_D3: CN3_A.13
SAMP_D4: CN3_B.12
SAMP_D5: CN3_A.12
SAMP_D6: CN3_B.11
SAMP_D7: CN3_A.11
SND_A1: CN3_A.22
SND_A2: CN3_A.21
SND_A3: CN3_B.21
SND_A4: CN3_A.20
SND_A5: CN3_B.20
SND_A6: CN3_B.19
SND_A7: CN3_A.19
SND_D0: CN3_A.23
SND_D1: CN3_B.23
SND_D2: CN3_A.24
SND_D3: CN3_A.25
SND_D4: CN3_A.26
SND_D5: CN3_A.27
SND_D6: CN3_A.28
SND_D7: CN3_A.29
SYNC: CN1_A.15
VBLANK: CN1_B.15
VCC: CN1_C.25, CN1_C.26, CN1_C.27, CN1_C.28, CN1_C.29, CN1_C.30, CN1_C.31, CN1_C.32, CN2_C.1, CN2_C.2, CN3_A.31, CN3_A.32, CN3_B.31, CN3_B.32
V_PULSE: CN2_B.3
~HINT: CN1_B.14
~IO_RD: CN1_B.11
~IO_WR: CN1_A.12
~LS245_EN: CN1_A.13
~MEM_RD: CN1_B.10
~MEM_WR: CN1_A.11
~PF_PRIO: CN1_A.17
~RESET: CN1_A.14
~SND_CS: CN3_B.16
~SND_INTP0: CN3_A.16
~SND_INTP1: CN3_B.15
~SND_OE: CN3_B.17
~SND_W: CN3_A.17
~V33_READY: CN1_B.13

Notes on the sheet:
Confirm?
Label direction represents board-to-board signal direction.
