wickerwaka/Arcade-IremM92_MiSTer/docs/m92_A-B_B-F/m92_A-B_B-F.kicad_sch

## KiCad design docs/m92_A-B_B-F/m92_A-B_B-F.kicad_sch (2023-03-26)

Schematic: m92_A-B_B-F.kicad_sch

Parts:
IC8: 7486
IC11, IC41, IC51: GAL16V8
IC20: 74153
IC21, IC29: 74LS273
IC37, IC38: MB81C78A; DIP-28_W15.24mm
IC40: 74LS04
IC52: 74LS32
IC56, IC57: 74LS245
IC58, IC59, IC60: 74LS244
IC61: 74LS139
IC62: 74LS20
RA18, RA19: 10K; R_Array_SIP9

Connections:
BUFFERB_A0: IC20.7 (Qa), IC37.23 (A0), IC38.23 (A0)
BUFFERB_A3: IC20.9 (Qb), IC37.21 (A3), IC38.21 (A3)
BUFFERB_A4: IC8.8, IC37.2 (A4), IC38.2 (A4)
BUFFER_A1: IC37.24 (A1), IC38.24 (A1)
BUFFER_A2: IC37.25 (A2), IC38.25 (A2)
BUFFER_A4: IC8.9, IC20.14 (A)
BUFFER_A5: IC37.3 (A5), IC38.3 (A5)
BUFFER_A6: IC37.4 (A6), IC38.4 (A6)
BUFFER_A7: IC37.5 (A7), IC38.5 (A7)
BUFFER_A8: IC37.6 (A8), IC38.6 (A8)
BUFFER_A9: IC37.7 (A9), IC38.7 (A9)
BUFFER_A10: IC37.8 (A10), IC38.8 (A10)
BUFFER_A11: IC37.9 (A11), IC38.9 (A11)
BUFFER_A12: IC37.10 (A12), IC38.10 (A12)
BUFFER_D0: IC37.11 (IO1)
BUFFER_D1: IC37.12 (IO2)
BUFFER_D2: IC37.13 (IO3)
BUFFER_D3: IC37.15 (IO4)
BUFFER_D4: IC37.16 (IO5)
BUFFER_D5: IC37.17 (IO6)
BUFFER_D6: IC37.18 (IO7)
BUFFER_D7: IC37.19 (IO8)
BUFFER_D8: IC38.11 (IO1)
BUFFER_D9: IC38.12 (IO2)
BUFFER_D10: IC38.13 (IO3)
BUFFER_D11: IC38.15 (IO4)
BUFFER_D12: IC38.16 (IO5)
BUFFER_D13: IC38.17 (IO6)
BUFFER_D14: IC38.18 (IO7)
BUFFER_D15: IC38.19 (IO8)
BUF_MREQ: IC41.2 (I2)
CN1_17A: IC11.5 (I5)
COIN_LATCH: IC61.11 (O1)
CPU_A0: IC60.3 (O3b)
CPU_A1: IC60.5 (O2b), IC61.14 (A0)
CPU_A2: IC60.7 (O1b)
CPU_A3: IC60.9 (O0b)
CPU_A4: IC60.18 (O0a)
CPU_A5: IC60.16 (O1a), IC61.2 (A0)
CPU_A6: IC60.14 (O2a), IC61.3 (A1)
CPU_A7: IC60.12 (O3a), IC61.1 (E)
CPU_A8: IC59.3 (O3b)
CPU_A9: IC59.5 (O2b)
CPU_A10: IC59.7 (O1b)
CPU_A11: IC41.14 (IO6), IC59.9 (O0b)
CPU_A12: IC41.13 (IO7), IC59.18 (O0a)
CPU_A13: IC41.11 (I10/~OE), IC59.16 (O1a)
CPU_A14: IC41.9 (I9), IC59.14 (O2a)
CPU_A15: IC41.8 (I8), IC59.12 (O3a)
CPU_A16: IC41.7 (I7), IC52.2, IC58.3 (O3b)
CPU_A17: IC41.6 (I6), IC58.5 (O2b), IC62.5
CPU_A18: IC41.5 (I5), IC58.7 (O1b), IC62.4
CPU_A19: IC41.4 (I4), IC58.9 (O0b), IC62.2
CPU_BUSST0: IC51.5 (I5)
CPU_BUSST1: IC51.4 (I4)
CPU_D0: IC21.8 (D3), IC56.9 (A7), RA18.2 (R1)
CPU_D1: IC21.13 (D4), IC56.8 (A6), RA18.3 (R2)
CPU_D2: IC21.7 (D2), IC56.7 (A5), RA18.4 (R3)
CPU_D3: IC21.14 (D5), IC56.6 (A4), RA18.5 (R4)
CPU_D4: IC21.4 (D1), IC56.5 (A3), RA18.6 (R5)
CPU_D5: IC21.17 (D6), IC56.4 (A2), RA18.7 (R6)
CPU_D6: IC21.3 (D0), IC56.3 (A1), RA18.8 (R7)
CPU_D7: IC21.18 (D7), IC56.2 (A0), RA18.9 (R8)
CPU_D8: IC29.8 (D3), IC57.9 (A7), RA19.2 (R1)
CPU_D9: IC29.13 (D4), IC57.8 (A6), RA19.3 (R2)
CPU_D10: IC29.7 (D2), IC57.7 (A5), RA19.4 (R3)
CPU_D11: IC29.14 (D5), IC57.6 (A4), RA19.5 (R4)
CPU_D12: IC29.4 (D1), IC57.5 (A3), RA19.6 (R5)
CPU_D13: IC29.17 (D6), IC57.4 (A2), RA19.7 (R6)
CPU_D14: IC29.3 (D0), IC57.3 (A1), RA19.8 (R7)
CPU_D15: IC29.18 (D7), IC57.2 (A0), RA19.9 (R8)
CPU_MREQ: IC51.1 (I1/CLK)
CPU_M/~IO: IC58.12 (O3a), IC62.1
CPU_R/~W: IC56.1 (A->B), IC57.1 (A->B), IC58.14 (O2a)
CPU_UBE: IC58.16 (O1a)
DMA_BUSY: IC11.6 (I6), IC20.2 (B)
IC42_136: IC11.7 (I7)
IC63_13: IC11.4 (I4)
IC63_158: IC11.3 (I3)
NC???: IC11.14 (IO6), IC11.15 (IO5)
unnamed: IC20.1 (~ENa), IC20.4 (I2a), IC20.6 (I0a), IC20.15 (~ENb)
unnamed: IC41.1 (I1/CLK), IC51.14 (IO6)
unnamed: IC52.1, IC62.6
unnamed: IC52.3, IC52.4, IC62.12
unnamed: IC58.1 (OEa), IC58.2 (I0a), IC58.10 (GND), IC58.19 (OEb)
unnamed: IC59.1 (OEa), IC59.10 (GND), IC59.19 (OEb)
unnamed: IC60.1 (OEa), IC60.10 (GND), IC60.19 (OEb)
unnamed: IC61.4 (O0), IC61.15 (E)
unnamed: IC62.9, IC62.10
OBJ_PAL_BANK: IC11.13 (IO7)
PIC_BUF~R/W: IC62.13
SELA0: IC11.18 (IO2)
SELB0: IC11.19 (IO1)
SND1_LATCH: IC61.12 (O0)
V33_A0: IC60.17 (I3b)
V33_A1: IC60.15 (I2b)
V33_A2: IC60.13 (I1b)
V33_A3: IC60.11 (I0b)
V33_A4: IC60.2 (I0a)
V33_A5: IC60.4 (I1a)
V33_A6: IC60.6 (I2a)
V33_A7: IC60.8 (I3a)
V33_A8: IC59.17 (I3b)
V33_A9: IC59.15 (I2b)
V33_A10: IC59.13 (I1b)
V33_A11: IC59.11 (I0b)
V33_A12: IC59.2 (I0a)
V33_A13: IC59.4 (I1a)
V33_A14: IC59.6 (I2a)
V33_A15: IC59.8 (I3a)
V33_A16: IC58.17 (I3b)
V33_A17: IC58.15 (I2b)
V33_A18: IC58.13 (I1b)
V33_A19: IC58.11 (I0b)
V33_D0: IC56.11 (B7)
V33_D1: IC56.12 (B6)
V33_D2: IC56.13 (B5)
V33_D3: IC56.14 (B4)
V33_D4: IC56.15 (B3)
V33_D5: IC56.16 (B2)
V33_D6: IC56.17 (B1)
V33_D7: IC56.18 (B0)
V33_D8: IC57.11 (B7)
V33_D9: IC57.12 (B6)
V33_D10: IC57.13 (B5)
V33_D11: IC57.14 (B4)
V33_D12: IC57.15 (B3)
V33_D13: IC57.16 (B2)
V33_D14: IC57.17 (B1)
V33_D15: IC57.18 (B0)
V33_M/~IO: IC58.8 (I3a)
V33_R/~W: IC58.6 (I2a)
V33_UBE: IC58.4 (I1a)
VID_CTRL0: IC20.10 (I0b), IC21.9 (Q3)
VID_CTRL1: IC20.11 (I1b), IC21.12 (Q4)
VID_CTRL2: IC20.5 (I1a), IC21.6 (Q2)
VID_CTRL3: IC20.12 (I2b), IC21.15 (Q5)
VID_CTRL4: IC20.13 (I3b), IC21.5 (Q1)
VID_CTRL5: IC20.3 (I3a), IC21.16 (Q6)
VID_CTRL6: IC11.11 (I10/~OE), IC21.2 (Q0)
VID_CTRL7: IC11.9 (I9), IC21.19 (Q7)
VID_CTRL8: IC29.9 (Q3)
VID_CTRL9: IC29.12 (Q4)
VID_CTRL10: IC29.6 (Q2)
VID_CTRL11: IC29.15 (Q5)
VID_CTRL12: IC11.8 (I8), IC29.5 (Q1)
VID_CTRL13: IC11.2 (I2), IC29.16 (Q6)
VID_CTRL14: IC29.2 (Q0)
VID_CTRL15: IC29.19 (Q7)
VID_CTRL_CLK: IC21.11 (Cp), IC29.11 (Cp), IC41.16 (IO4)
~BUFFER_CS: IC37.20 (~CS1), IC38.20 (~CS1)
~BUFFER_WE: IC37.27 (~WE), IC38.27 (~WE)
~CPU_BCYST: IC51.8 (I8)
~CPU_WE: IC51.2 (I2)
~IO_RD: IC51.17 (I03)
~IO_WR: IC51.16 (IO4), IC61.13 (A1)
~LS245_EN: IC56.19 (CE), IC57.19 (CE), IC62.8
~MEM_RD: IC51.19 (IO1)
~MEM_WR: IC41.15 (IO5), IC51.18 (IO2)
~PALOBJ_WR: IC41.17 (I03)
~PIC_INTAK: IC51.12 (IO8)
~RESET: IC21.1 (~Mr), IC29.1 (~Mr)
~V33_DSTB: IC51.7 (I7)
~VID_CTRL6: IC11.12 (IO8)

Notes on the sheet:
Audio Stuff
Disable data bus buffers when reading from RAM (0xeXXXX) and when the PIC is sending vector to CPU.
