wickerwaka/Arcade-IremM92_MiSTer/docs/m92_A-B_B-F/palette_ram.kicad_sch

## KiCad design docs/m92_A-B_B-F/palette_ram.kicad_sch (2023-03-26)

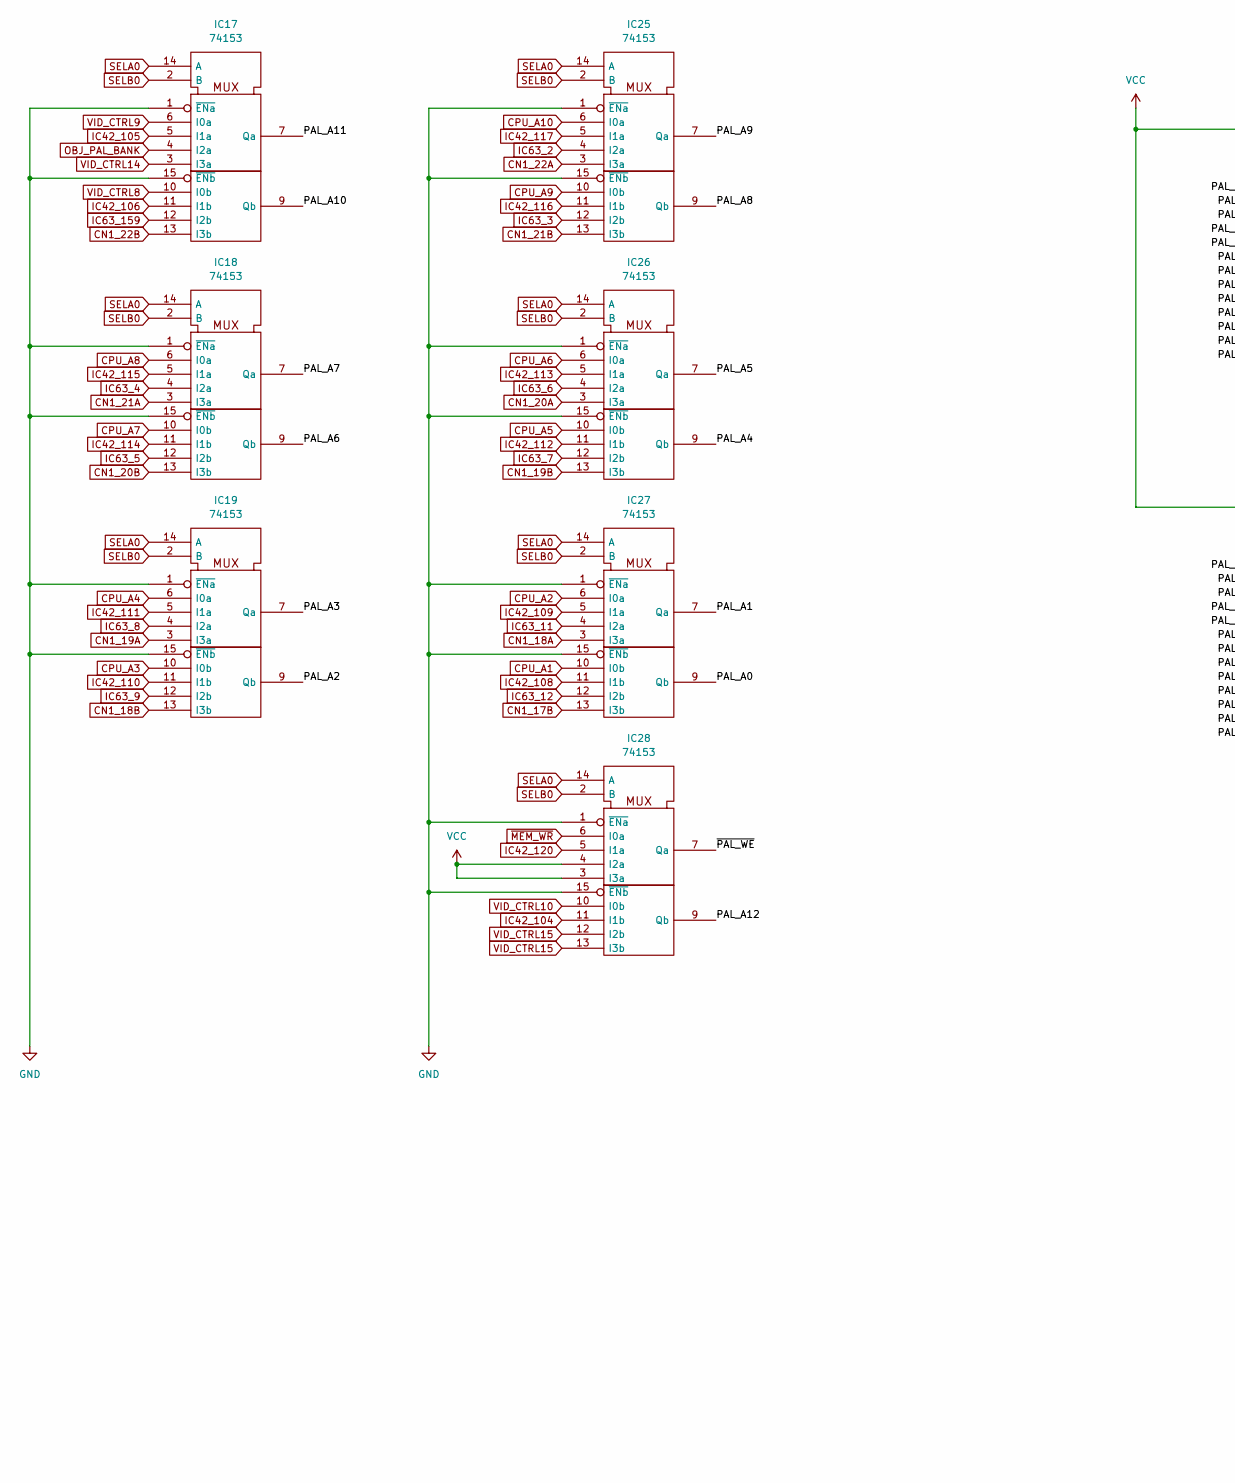
[picture p15: schematic palette_ram.kicad_sch, part in row 1, column 1]

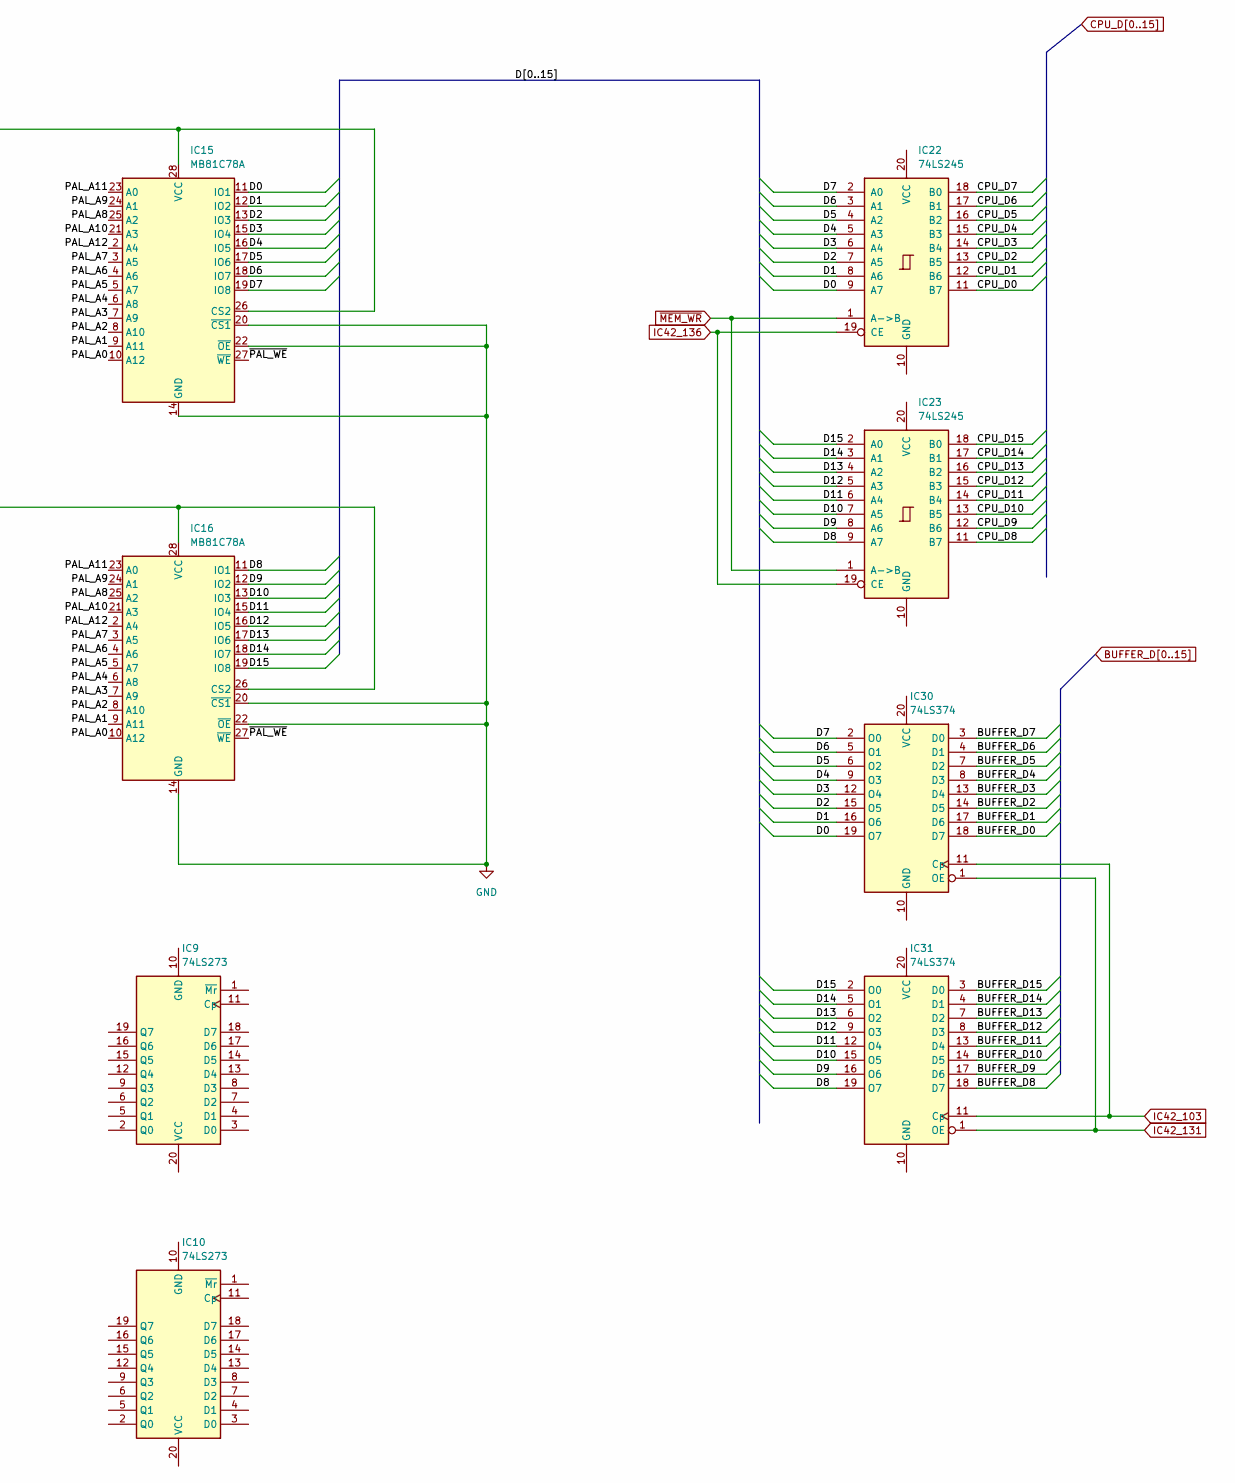
[picture p16: schematic palette_ram.kicad_sch, part in row 1, column 2]

Parts:
IC9, IC10: 74LS273
IC15, IC16: MB81C78A; DIP-28_W15.24mm
IC17, IC18, IC19, IC25, IC26, IC27, IC28: 74153
IC22, IC23: 74LS245
IC30, IC31: 74LS374

Connections:
BUFFER_D0: IC30.18 (D7)
BUFFER_D1: IC30.17 (D6)
BUFFER_D2: IC30.14 (D5)
BUFFER_D3: IC30.13 (D4)
BUFFER_D4: IC30.8 (D3)
BUFFER_D5: IC30.7 (D2)
BUFFER_D6: IC30.4 (D1)
BUFFER_D7: IC30.3 (D0)
BUFFER_D8: IC31.18 (D7)
BUFFER_D9: IC31.17 (D6)
BUFFER_D10: IC31.14 (D5)
BUFFER_D11: IC31.13 (D4)
BUFFER_D12: IC31.8 (D3)
BUFFER_D13: IC31.7 (D2)
BUFFER_D14: IC31.4 (D1)
BUFFER_D15: IC31.3 (D0)
CN1_17B: IC27.13 (I3b)
CN1_18A: IC27.3 (I3a)
CN1_18B: IC19.13 (I3b)
CN1_19A: IC19.3 (I3a)
CN1_19B: IC26.13 (I3b)
CN1_20A: IC26.3 (I3a)
CN1_20B: IC18.13 (I3b)
CN1_21A: IC18.3 (I3a)
CN1_21B: IC25.13 (I3b)
CN1_22A: IC25.3 (I3a)
CN1_22B: IC17.13 (I3b)
CPU_A1: IC27.10 (I0b)
CPU_A2: IC27.6 (I0a)
CPU_A3: IC19.10 (I0b)
CPU_A4: IC19.6 (I0a)
CPU_A5: IC26.10 (I0b)
CPU_A6: IC26.6 (I0a)
CPU_A7: IC18.10 (I0b)
CPU_A8: IC18.6 (I0a)
CPU_A9: IC25.10 (I0b)
CPU_A10: IC25.6 (I0a)
CPU_D0: IC22.11 (B7)
CPU_D1: IC22.12 (B6)
CPU_D2: IC22.13 (B5)
CPU_D3: IC22.14 (B4)
CPU_D4: IC22.15 (B3)
CPU_D5: IC22.16 (B2)
CPU_D6: IC22.17 (B1)
CPU_D7: IC22.18 (B0)
CPU_D8: IC23.11 (B7)
CPU_D9: IC23.12 (B6)
CPU_D10: IC23.13 (B5)
CPU_D11: IC23.14 (B4)
CPU_D12: IC23.15 (B3)
CPU_D13: IC23.16 (B2)
CPU_D14: IC23.17 (B1)
CPU_D15: IC23.18 (B0)
D0: IC15.11 (IO1), IC22.9 (A7), IC30.19 (O7)
D1: IC15.12 (IO2), IC22.8 (A6), IC30.16 (O6)
D2: IC15.13 (IO3), IC22.7 (A5), IC30.15 (O5)
D3: IC15.15 (IO4), IC22.6 (A4), IC30.12 (O4)
D4: IC15.16 (IO5), IC22.5 (A3), IC30.9 (O3)
D5: IC15.17 (IO6), IC22.4 (A2), IC30.6 (O2)
D6: IC15.18 (IO7), IC22.3 (A1), IC30.5 (O1)
D7: IC15.19 (IO8), IC22.2 (A0), IC30.2 (O0)
D8: IC16.11 (IO1), IC23.9 (A7), IC31.19 (O7)
D9: IC16.12 (IO2), IC23.8 (A6), IC31.16 (O6)
D10: IC16.13 (IO3), IC23.7 (A5), IC31.15 (O5)
D11: IC16.15 (IO4), IC23.6 (A4), IC31.12 (O4)
D12: IC16.16 (IO5), IC23.5 (A3), IC31.9 (O3)
D13: IC16.17 (IO6), IC23.4 (A2), IC31.6 (O2)
D14: IC16.18 (IO7), IC23.3 (A1), IC31.5 (O1)
D15: IC16.19 (IO8), IC23.2 (A0), IC31.2 (O0)
IC42_103: IC30.11 (Cp), IC31.11 (Cp)
IC42_104: IC28.11 (I1b)
IC42_105: IC17.5 (I1a)
IC42_106: IC17.11 (I1b)
IC42_108: IC27.11 (I1b)
IC42_109: IC27.5 (I1a)
IC42_110: IC19.11 (I1b)
IC42_111: IC19.5 (I1a)
IC42_112: IC26.11 (I1b)
IC42_113: IC26.5 (I1a)
IC42_114: IC18.11 (I1b)
IC42_115: IC18.5 (I1a)
IC42_116: IC25.11 (I1b)
IC42_117: IC25.5 (I1a)
IC42_120: IC28.5 (I1a)
IC42_131: IC30.1 (OE), IC31.1 (OE)
IC42_136: IC22.19 (CE), IC23.19 (CE)
IC63_2: IC25.4 (I2a)
IC63_3: IC25.12 (I2b)
IC63_4: IC18.4 (I2a)
IC63_5: IC18.12 (I2b)
IC63_6: IC26.4 (I2a)
IC63_7: IC26.12 (I2b)
IC63_8: IC19.4 (I2a)
IC63_9: IC19.12 (I2b)
IC63_11: IC27.4 (I2a)
IC63_12: IC27.12 (I2b)
IC63_159: IC17.12 (I2b)
unnamed: IC15.14 (GND), IC15.20 (~CS1), IC15.22 (~OE), IC16.14 (GND), IC16.20 (~CS1), IC16.22 (~OE)
unnamed: IC15.26 (CS2), IC15.28 (VCC), IC16.26 (CS2), IC16.28 (VCC)
unnamed: IC17.1 (~ENa), IC17.15 (~ENb), IC18.1 (~ENa), IC18.15 (~ENb), IC19.1 (~ENa), IC19.15 (~ENb)
unnamed: IC25.1 (~ENa), IC25.15 (~ENb), IC26.1 (~ENa), IC26.15 (~ENb), IC27.1 (~ENa), IC27.15 (~ENb), IC28.1 (~ENa), IC28.15 (~ENb)
unnamed: IC28.3 (I3a), IC28.4 (I2a)
OBJ_PAL_BANK: IC17.4 (I2a)
PAL_A0: IC15.10 (A12), IC16.10 (A12), IC27.9 (Qb)
PAL_A1: IC15.9 (A11), IC16.9 (A11), IC27.7 (Qa)
PAL_A2: IC15.8 (A10), IC16.8 (A10), IC19.9 (Qb)
PAL_A3: IC15.7 (A9), IC16.7 (A9), IC19.7 (Qa)
PAL_A4: IC15.6 (A8), IC16.6 (A8), IC26.9 (Qb)
PAL_A5: IC15.5 (A7), IC16.5 (A7), IC26.7 (Qa)
PAL_A6: IC15.4 (A6), IC16.4 (A6), IC18.9 (Qb)
PAL_A7: IC15.3 (A5), IC16.3 (A5), IC18.7 (Qa)
PAL_A8: IC15.25 (A2), IC16.25 (A2), IC25.9 (Qb)
PAL_A9: IC15.24 (A1), IC16.24 (A1), IC25.7 (Qa)
PAL_A10: IC15.21 (A3), IC16.21 (A3), IC17.9 (Qb)
PAL_A11: IC15.23 (A0), IC16.23 (A0), IC17.7 (Qa)
PAL_A12: IC15.2 (A4), IC16.2 (A4), IC28.9 (Qb)
SELA0: IC17.14 (A), IC18.14 (A), IC19.14 (A), IC25.14 (A), IC26.14 (A), IC27.14 (A), IC28.14 (A)
SELB0: IC17.2 (B), IC18.2 (B), IC19.2 (B), IC25.2 (B), IC26.2 (B), IC27.2 (B), IC28.2 (B)
VID_CTRL8: IC17.10 (I0b)
VID_CTRL9: IC17.6 (I0a)
VID_CTRL10: IC28.10 (I0b)
VID_CTRL14: IC17.3 (I3a)
VID_CTRL15: IC28.12 (I2b), IC28.13 (I3b)
~MEM_WR: IC22.1 (A->B), IC23.1 (A->B), IC28.6 (I0a)
~PAL_WE: IC15.27 (~WE), IC16.27 (~WE), IC28.7 (Qa)
