wickerwaka/Arcade-IremM92_MiSTer/docs/m92_A-B_B-F/sample_filters.kicad_sch

## KiCad design docs/m92_A-B_B-F/sample_filters.kicad_sch (2023-03-26)

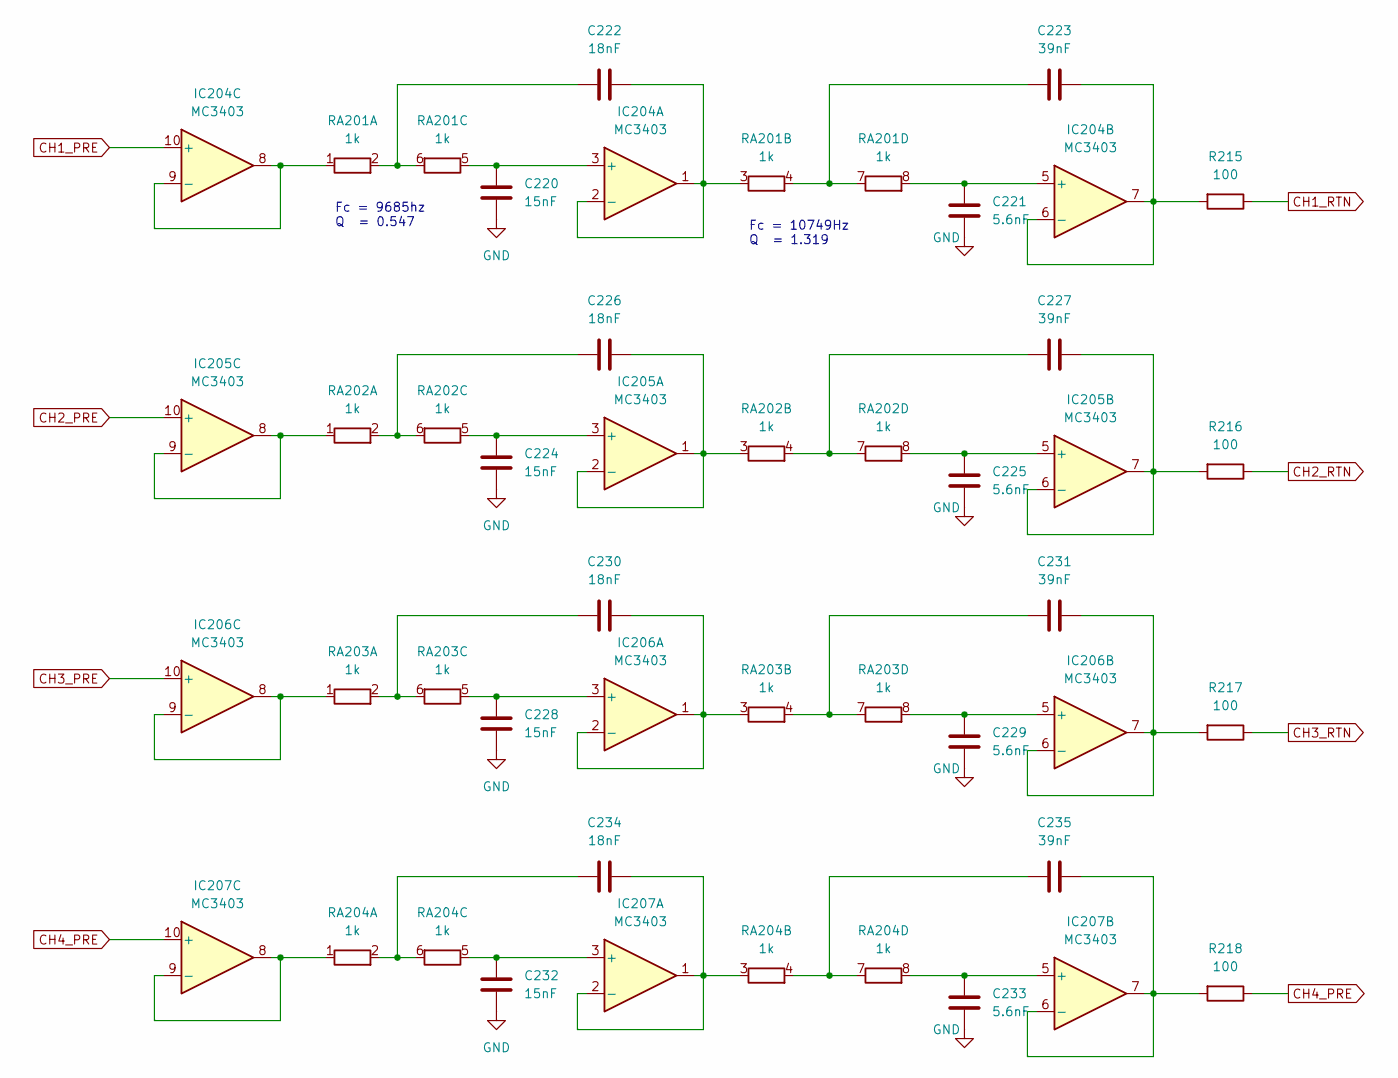
[picture p17: schematic sample_filters.kicad_sch]

Parts:
C220, C224, C228, C232: 15nF
C221, C225, C229, C233: 5.6nF
C222, C226, C230, C234: 18nF
C223, C227, C231, C235: 39nF
IC204, IC205, IC206, IC207: MC3403
R215, R216, R217, R218: 100
RA201, RA202, RA203, RA204: 1k; R_Array_SIP8

Connections:
CH1_PRE: IC204.10 (+)
CH1_RTN: R215.1
CH2_PRE: IC205.10 (+)
CH2_RTN: R216.1
CH3_PRE: IC206.10 (+)
CH3_RTN: R217.1
CH4_PRE: IC207.10 (+), R218.1
unnamed: C220.1, IC204.3 (+), RA201.5 (R3.1)
unnamed: C221.1, IC204.5 (+), RA201.8 (R4.2)
unnamed: C222.1, RA201.2 (R1.2), RA201.6 (R3.2)
unnamed: C222.2, IC204.1, IC204.2 (-), RA201.3 (R2.1)
unnamed: C223.1, RA201.4 (R2.2), RA201.7 (R4.1)
unnamed: C223.2, IC204.6 (-), IC204.7, R215.2
unnamed: C224.1, IC205.3 (+), RA202.5 (R3.1)
unnamed: C225.1, IC205.5 (+), RA202.8 (R4.2)
unnamed: C226.1, RA202.2 (R1.2), RA202.6 (R3.2)
unnamed: C226.2, IC205.1, IC205.2 (-), RA202.3 (R2.1)
unnamed: C227.1, RA202.4 (R2.2), RA202.7 (R4.1)
unnamed: C227.2, IC205.6 (-), IC205.7, R216.2
unnamed: C228.1, IC206.3 (+), RA203.5 (R3.1)
unnamed: C229.1, IC206.5 (+), RA203.8 (R4.2)
unnamed: C230.1, RA203.2 (R1.2), RA203.6 (R3.2)
unnamed: C230.2, IC206.1, IC206.2 (-), RA203.3 (R2.1)
unnamed: C231.1, RA203.4 (R2.2), RA203.7 (R4.1)
unnamed: C231.2, IC206.6 (-), IC206.7, R217.2
unnamed: C232.1, IC207.3 (+), RA204.5 (R3.1)
unnamed: C233.1, IC207.5 (+), RA204.8 (R4.2)
unnamed: C234.1, RA204.2 (R1.2), RA204.6 (R3.2)
unnamed: C234.2, IC207.1, IC207.2 (-), RA204.3 (R2.1)
unnamed: C235.1, RA204.4 (R2.2), RA204.7 (R4.1)
unnamed: C235.2, IC207.6 (-), IC207.7, R218.2
unnamed: IC204.8, IC204.9 (-), RA201.1 (R1.1)
unnamed: IC205.8, IC205.9 (-), RA202.1 (R1.1)
unnamed: IC206.8, IC206.9 (-), RA203.1 (R1.1)
unnamed: IC207.8, IC207.9 (-), RA204.1 (R1.1)

Notes on the sheet:
Fc = 9685hz Q = 0.547
Fc = 10749Hz Q = 1.319
