wickerwaka/Arcade-IremM92_MiSTer/docs/m92_A-B_B-F/vram.kicad_sch

## KiCad design docs/m92_A-B_B-F/vram.kicad_sch (2023-03-26)

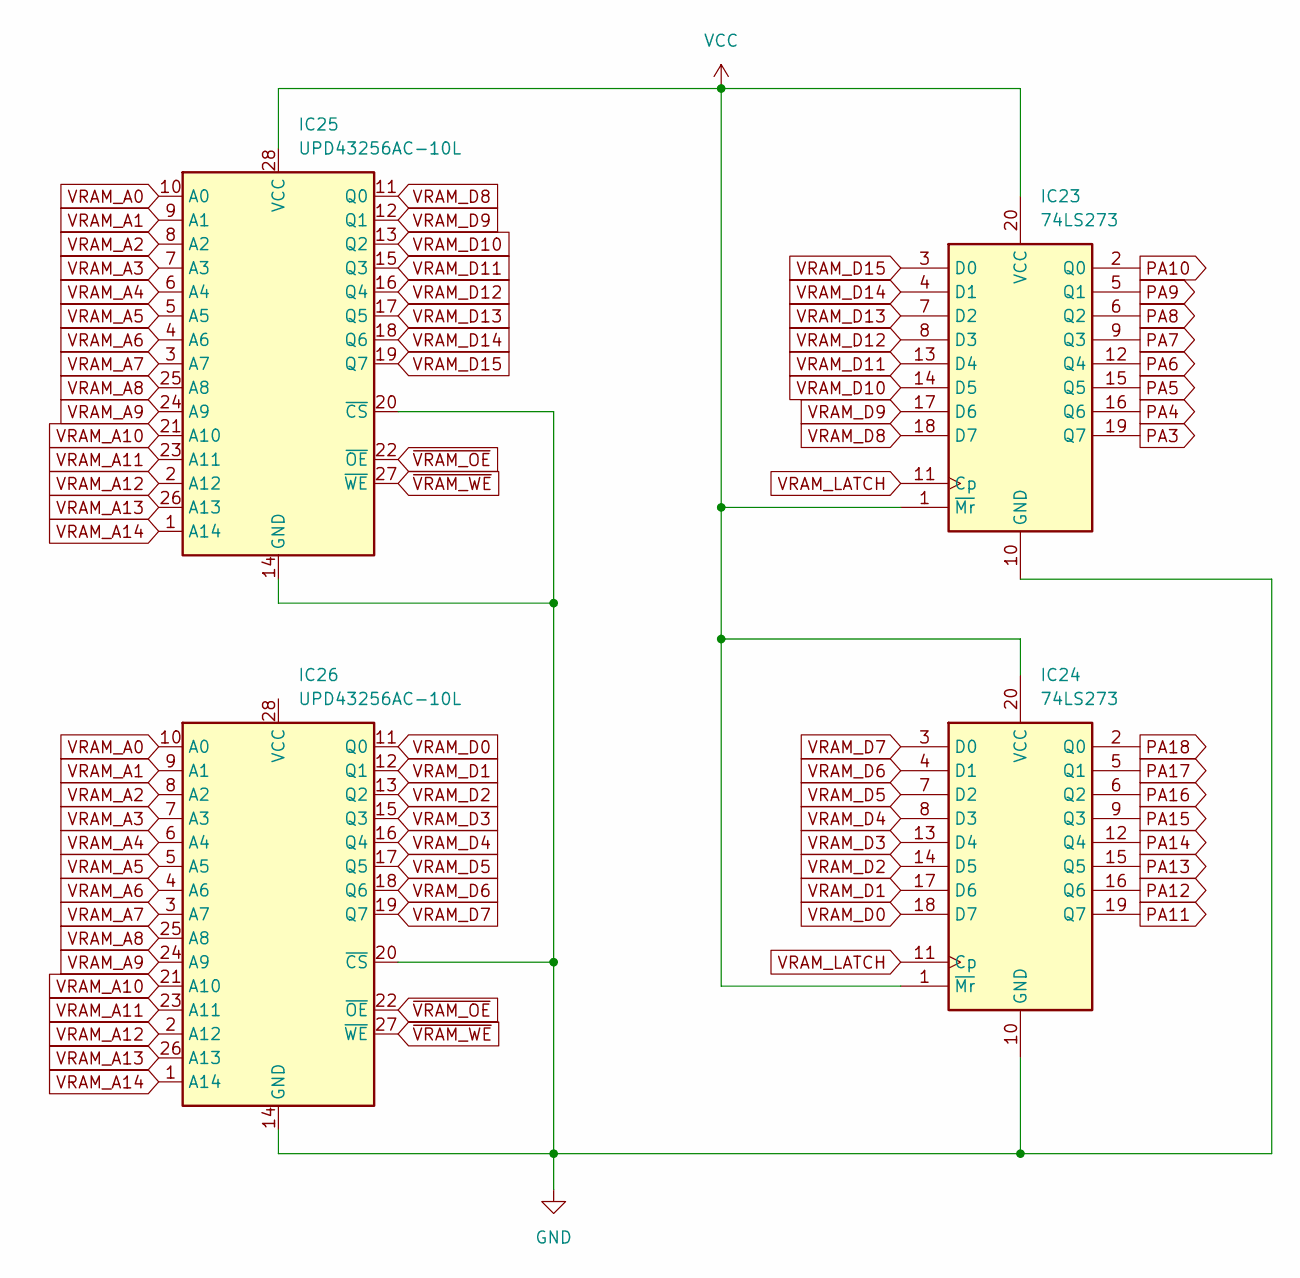
[picture p18: schematic vram.kicad_sch]

Parts:
IC23, IC24: 74LS273
IC25, IC26: UPD43256AC-10L; DIP-28_W15.24mm

Connections:
unnamed: IC23.1 (~Mr), IC23.20 (VCC), IC24.1 (~Mr), IC24.20 (VCC), IC25.28 (VCC)
unnamed: IC23.10 (GND), IC24.10 (GND), IC25.14 (GND), IC25.20 (~CS), IC26.14 (GND), IC26.20 (~CS)
PA3: IC23.19 (Q7)
PA4: IC23.16 (Q6)
PA5: IC23.15 (Q5)
PA6: IC23.12 (Q4)
PA7: IC23.9 (Q3)
PA8: IC23.6 (Q2)
PA9: IC23.5 (Q1)
PA10: IC23.2 (Q0)
PA11: IC24.19 (Q7)
PA12: IC24.16 (Q6)
PA13: IC24.15 (Q5)
PA14: IC24.12 (Q4)
PA15: IC24.9 (Q3)
PA16: IC24.6 (Q2)
PA17: IC24.5 (Q1)
PA18: IC24.2 (Q0)
VRAM_A0: IC25.10 (A0), IC26.10 (A0)
VRAM_A1: IC25.9 (A1), IC26.9 (A1)
VRAM_A2: IC25.8 (A2), IC26.8 (A2)
VRAM_A3: IC25.7 (A3), IC26.7 (A3)
VRAM_A4: IC25.6 (A4), IC26.6 (A4)
VRAM_A5: IC25.5 (A5), IC26.5 (A5)
VRAM_A6: IC25.4 (A6), IC26.4 (A6)
VRAM_A7: IC25.3 (A7), IC26.3 (A7)
VRAM_A8: IC25.25 (A8), IC26.25 (A8)
VRAM_A9: IC25.24 (A9), IC26.24 (A9)
VRAM_A10: IC25.21 (A10), IC26.21 (A10)
VRAM_A11: IC25.23 (A11), IC26.23 (A11)
VRAM_A12: IC25.2 (A12), IC26.2 (A12)
VRAM_A13: IC25.26 (A13), IC26.26 (A13)
VRAM_A14: IC25.1 (A14), IC26.1 (A14)
VRAM_D0: IC24.18 (D7), IC26.11 (Q0)
VRAM_D1: IC24.17 (D6), IC26.12 (Q1)
VRAM_D2: IC24.14 (D5), IC26.13 (Q2)
VRAM_D3: IC24.13 (D4), IC26.15 (Q3)
VRAM_D4: IC24.8 (D3), IC26.16 (Q4)
VRAM_D5: IC24.7 (D2), IC26.17 (Q5)
VRAM_D6: IC24.4 (D1), IC26.18 (Q6)
VRAM_D7: IC24.3 (D0), IC26.19 (Q7)
VRAM_D8: IC23.18 (D7), IC25.11 (Q0)
VRAM_D9: IC23.17 (D6), IC25.12 (Q1)
VRAM_D10: IC23.14 (D5), IC25.13 (Q2)
VRAM_D11: IC23.13 (D4), IC25.15 (Q3)
VRAM_D12: IC23.8 (D3), IC25.16 (Q4)
VRAM_D13: IC23.7 (D2), IC25.17 (Q5)
VRAM_D14: IC23.4 (D1), IC25.18 (Q6)
VRAM_D15: IC23.3 (D0), IC25.19 (Q7)
VRAM_LATCH: IC23.11 (Cp), IC24.11 (Cp)
~VRAM_OE: IC25.22 (~OE), IC26.22 (~OE)
~VRAM_WE: IC25.27 (~WE), IC26.27 (~WE)
