wickerwaka/Arcade-IremM92_MiSTer/Arcade-IremM92.sv

//============================================================================
//  Irem M92 for MiSTer FPGA
//
//  Copyright (C) 2023 Martin Donlon
//
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

import m92_pkg::*;

module emu
(
    //Master input clock
    input         CLK_50M,

    //Async reset from top-level module.
    //Can be used as initial reset.
    input         RESET,

    //Must be passed to hps_io module
    inout  [48:0] HPS_BUS,

    //Base video clock. Usually equals to CLK_SYS.
    output        CLK_VIDEO,

    //Multiple resolutions are supported using different CE_PIXEL rates.
    //Must be based on CLK_VIDEO
    output        CE_PIXEL,

    //Video aspect ratio for HDMI. Most retro systems have ratio 4:3.
    //if VIDEO_ARX[12] or VIDEO_ARY[12] is set then [11:0] contains scaled size instead of aspect ratio.
    output [12:0] VIDEO_ARX,
    output [12:0] VIDEO_ARY,

    output  [7:0] VGA_R,
    output  [7:0] VGA_G,
    output  [7:0] VGA_B,
    output        VGA_HS,
    output        VGA_VS,
    output        VGA_DE,    // = ~(VBlank | HBlank)
    output        VGA_F1,
    output [1:0]  VGA_SL,
    output        VGA_SCALER, // Force VGA scaler
    output        VGA_DISABLE,

    input  [11:0] HDMI_WIDTH,
    input  [11:0] HDMI_HEIGHT,
    output        HDMI_FREEZE,

`ifdef MISTER_FB
    // Use framebuffer in DDRAM (USE_FB=1 in qsf)
    // FB_FORMAT:
    //    [2:0] : 011=8bpp(palette) 100=16bpp 101=24bpp 110=32bpp
    //    [3]   : 0=16bits 565 1=16bits 1555
    //    [4]   : 0=RGB  1=BGR (for 16/24/32 modes)
    //
    // FB_STRIDE either 0 (rounded to 256 bytes) or multiple of pixel size (in bytes)
    output        FB_EN,
    output  [4:0] FB_FORMAT,
    output [11:0] FB_WIDTH,
    output [11:0] FB_HEIGHT,
    output [31:0] FB_BASE,
    output [13:0] FB_STRIDE,
    input         FB_VBL,
    input         FB_LL,
    output        FB_FORCE_BLANK,

`ifdef MISTER_FB_PALETTE
    // Palette control for 8bit modes.
    // Ignored for other video modes.
    output        FB_PAL_CLK,
    output  [7:0] FB_PAL_ADDR,
    output [23:0] FB_PAL_DOUT,
    input  [23:0] FB_PAL_DIN,
    output        FB_PAL_WR,
`endif
`endif

    output        LED_USER,  // 1 - ON, 0 - OFF.

    // b[1]: 0 - LED status is system status OR'd with b[0]
    //       1 - LED status is controled solely by b[0]
    // hint: supply 2'b00 to let the system control the LED.
    output  [1:0] LED_POWER,
    output  [1:0] LED_DISK,

    // I/O board button press simulation (active high)
    // b[1]: user button
    // b[0]: osd button
    output  [1:0] BUTTONS,

    input         CLK_AUDIO, // 24.576 MHz
    output [15:0] AUDIO_L,
    output [15:0] AUDIO_R,
    output        AUDIO_S,   // 1 - signed audio samples, 0 - unsigned
    output  [1:0] AUDIO_MIX, // 0 - no mix, 1 - 25%, 2 - 50%, 3 - 100% (mono)

    //ADC
    inout   [3:0] ADC_BUS,

    //SD-SPI
    output        SD_SCK,
    output        SD_MOSI,
    input         SD_MISO,
    output        SD_CS,
    input         SD_CD,

    //High latency DDR3 RAM interface
    //Use for non-critical time purposes
    output        DDRAM_CLK,
    input         DDRAM_BUSY,
    output  [7:0] DDRAM_BURSTCNT,
    output [28:0] DDRAM_ADDR,
    input  [63:0] DDRAM_DOUT,
    input         DDRAM_DOUT_READY,
    output        DDRAM_RD,
    output [63:0] DDRAM_DIN,
    output  [7:0] DDRAM_BE,
    output        DDRAM_WE,

    //SDRAM interface with lower latency
    output        SDRAM_CLK,
    output        SDRAM_CKE,
    output [12:0] SDRAM_A,
    output  [1:0] SDRAM_BA,
    inout  [15:0] SDRAM_DQ,
    output        SDRAM_DQML,
    output        SDRAM_DQMH,
    output        SDRAM_nCS,
    output        SDRAM_nCAS,
    output        SDRAM_nRAS,
    output        SDRAM_nWE,

`ifdef MISTER_DUAL_SDRAM
    //Secondary SDRAM
    //Set all output SDRAM_* signals to Z ASAP if SDRAM2_EN is 0
    input         SDRAM2_EN,
    output        SDRAM2_CLK,
    output [12:0] SDRAM2_A,
    output  [1:0] SDRAM2_BA,
    inout  [15:0] SDRAM2_DQ,
    output        SDRAM2_nCS,
    output        SDRAM2_nCAS,
    output        SDRAM2_nRAS,
    output        SDRAM2_nWE,
`endif

    input         UART_CTS,
    output        UART_RTS,
    input         UART_RXD,
    output        UART_TXD,
    output        UART_DTR,
    input         UART_DSR,

    // Open-drain User port.
    // 0 - D+/RX
    // 1 - D-/TX
    // 2..6 - USR2..USR6
    // Set USER_OUT to 1 to read from USER_IN.
    input   [6:0] USER_IN,
    output  [6:0] USER_OUT,

    input         OSD_STATUS
);

///////// Default values for ports not used in this core /////////

assign ADC_BUS  = 'Z;
assign USER_OUT = '1;
assign {UART_RTS, UART_TXD, UART_DTR} = 0;
assign {SD_SCK, SD_MOSI, SD_CS} = 'Z;
assign CLK_VIDEO = clk_sys;

assign VGA_F1 = 0;
assign VGA_SCALER = 0;
assign VGA_DISABLE = 0;

assign AUDIO_S = 1;
assign AUDIO_MIX = 0;

assign LED_DISK = 0;
assign LED_POWER = 0;
assign BUTTONS = 0;

//////////////////////////////////////////////////////////////////

wire [1:0] ar = status[2:1];
wire [1:0] scandoubler_fx = status[4:3];
wire [1:0] scale = status[6:5];
wire pause_in_osd = status[7];
wire system_pause;

assign VGA_SL = scandoubler_fx;
assign HDMI_FREEZE = 0; //system_pause;

wire [2:0] dbg_en_layers = ~status[66:64];
wire dbg_solid_sprites = status[67];
wire en_sprites = 1;
wire dbg_sprite_freeze = 0;

`include "build_id.v" 
localparam CONF_STR = {
    "IremM92;;",
    "-;",
    "P1,Video Settings;",
    "P1O[2:1],Aspect ratio,Original,Full Screen,[ARC1],[ARC2];",
    "P1O[4:3],Scandoubler Fx,None,CRT 25%,CRT 50%,CRT 75%;",
    "P1O[6:5],Scale,Normal,V-Integer,Narrower HV-Integer,Wider HV-Integer;",
    "P1-;",
    "P1O[10],Orientation,Horz,Vert;",
    "P1-;",
    "d1P1O[11],240p Crop,Off,On;",
    "d2P1O[16:12],Crop Offset,0,1,2,3,4,5,6,7,8,-8,-7,-6,-5,-4,-3,-2,-1;",
    "P1-;",
    "P1O[21:17],Analog Video H-Pos,0,1,2,3,4,5,6,7,8,9,10,11,12,13,14,15,16,-15,-14,-13,-12,-11,-10,-9,-8,-7,-6,-5,-4,-3,-2,-1;",
    "P1O[26:22],Analog Video V-Pos,0,1,2,3,4,5,6,7,8,9,10,11,12,13,14,15,16,-15,-14,-13,-12,-11,-10,-9,-8,-7,-6,-5,-4,-3,-2,-1;",
    "-;",
    "O[7],OSD Pause,Off,On;",
    "-;",
    "O[8],Autosave Score Data,Off,On;",
    "-;",
    "DIP;",
    "-;",
    "P2,Debug;",
    "P2-;",
    "P2O[64],Layer 1,On,Off;",
    "P2O[65],Layer 2,On,Off;",
    "P2O[66],Layer 3,On,Off;",
    "P2O[67],Solid Sprites,Off,On;",
    "-;",
    "T[0],Reset;",
    "DEFMRA,/_Arcade/m92.mra;",
    "V,v",`BUILD_DATE 
};

wire        forced_scandoubler;
wire  [1:0] buttons;
wire [128:0] status;
wire [10:0] ps2_key;

wire ioctl_rom_wait;
wire ioctl_dbg_wait;
wire ioctl_hs_upload_req;
wire ioctl_m92_upload_req;
wire [7:0] ioctl_hs_din;
wire [7:0] ioctl_m92_din;

wire        ioctl_download;
wire        ioctl_upload;
wire        ioctl_upload_req = ioctl_hs_upload_req | ioctl_m92_upload_req;
wire  [7:0] ioctl_index;
wire  [7:0] ioctl_upload_index;
wire        ioctl_wr;
wire        ioctl_rd;
wire [24:0] ioctl_addr;
wire  [7:0] ioctl_dout;
wire  [7:0] ioctl_din = ioctl_m92_din | ioctl_hs_din;
wire        ioctl_wait = ioctl_rom_wait | ioctl_dbg_wait;

wire [15:0] joystick_p1, joystick_p2, joystick_p3, joystick_p4;

wire [21:0] gamma_bus;
wire        direct_video;
wire        video_rotated;
wire        no_rotate = ~status[10];
wire        flip = 0;
wire        rotate_ccw = 1;

wire        autosave = status[8];

wire        allow_crop_240p = ~forced_scandoubler && scale == 0;
wire        crop_240p = allow_crop_240p & status[11];
wire [4:0]  crop_offset = status[16:12] < 9 ? {status[16:12]} : ( status[16:12] + 5'd15 );


hps_io #(.CONF_STR(CONF_STR)) hps_io
(
    .clk_sys(clk_sys),
    .HPS_BUS(HPS_BUS),
    .EXT_BUS(),
    .gamma_bus(gamma_bus),
    .direct_video(direct_video),

    .forced_scandoubler(forced_scandoubler),
    .new_vmode(0),
    .video_rotated(video_rotated),

    .buttons(buttons),
    .status(status),
    .status_menumask({crop_240p, allow_crop_240p, direct_video}),

    .ioctl_download(ioctl_download),
    .ioctl_upload(ioctl_upload),
    .ioctl_upload_index(ioctl_upload_index),
    .ioctl_upload_req(ioctl_upload_req & autosave),
    .ioctl_wr(ioctl_wr),
    .ioctl_rd(ioctl_rd),
    .ioctl_addr(ioctl_addr),
    .ioctl_dout(ioctl_dout),
    .ioctl_din(ioctl_din),
    .ioctl_index(ioctl_index),
    .ioctl_wait(ioctl_wait),

    .joystick_0(joystick_p1),
    .joystick_1(joystick_p2),
    .joystick_2(joystick_p3),
    .joystick_3(joystick_p4),

    .ps2_key(ps2_key)
);

///////////////////////   CLOCKS   ///////////////////////////////

wire clk_sys;
wire clk_ram;
wire pll_locked;
pll pll
(
    .refclk(CLK_50M),
    .rst(0),
    .outclk_0(clk_ram),
    .outclk_1(clk_sys),
    .locked(pll_locked)
);

wire reset = RESET | status[0] | buttons[1];

///////////////////////////////////////////////////////////////////////
// SDRAM
///////////////////////////////////////////////////////////////////////
wire [63:0] sdr_sprite_dout;
wire [24:0] sdr_sprite_addr;
wire sdr_sprite_req, sdr_sprite_rdy, sdr_sprite_refresh;

wire [31:0] sdr_bg_dout;
wire [24:0] sdr_bg_addr;
wire sdr_bg_req, sdr_bg_rdy;

wire [63:0] sdr_audio_dout;
wire [24:0] sdr_audio_addr;
wire sdr_audio_req, sdr_audio_rdy;

wire [15:0] sdr_cpu_dout, sdr_cpu_din;
wire [24:0] sdr_cpu_addr;
wire sdr_cpu_req;
wire [1:0] sdr_cpu_wr_sel;

reg [24:0] sdr_rom_addr;
reg [15:0] sdr_rom_data;
reg [1:0] sdr_rom_be;
reg sdr_rom_req;

wire sdr_rom_write = ioctl_download && (ioctl_index == 0);

wire sdr_hs_req;
wire sdr_hs_rq;
wire sdr_hs_rq2;
wire sdr_hs_ack;
wire [1:0] sdr_hs_wr_sel;
wire [24:0] sdr_hs_addr;
wire [15:0] sdr_hs_din; 
wire hs_mem_read_lat;
wire hs_mem_write_lat;
wire hs_mem_rq_active;


wire [24:0] sdr_ch3_addr = sdr_rom_write ? sdr_rom_addr : hs_mem_rq_active ? sdr_hs_addr : sdr_cpu_addr;
wire [15:0] sdr_ch3_din = sdr_rom_write ? sdr_rom_data : hs_mem_rq_active ? sdr_hs_din : sdr_cpu_din;
wire [1:0] sdr_ch3_be = sdr_rom_write ? sdr_rom_be : hs_mem_rq_active ? sdr_hs_wr_sel : sdr_cpu_wr_sel;
wire sdr_ch3_rnw = sdr_rom_write ? 1'b0 : hs_mem_rq_active ? ~{|sdr_hs_wr_sel} : ~{|sdr_cpu_wr_sel};
wire sdr_ch3_req = sdr_rom_write ? sdr_rom_req : hs_mem_rq_active ? sdr_hs_req : sdr_cpu_req;
wire sdr_ch3_rdy;
wire sdr_cpu_rdy = sdr_ch3_rdy;
wire sdr_rom_rdy = sdr_ch3_rdy;
wire sdr_hs_rdy = sdr_ch3_rdy;

wire [19:0] bram_addr;
wire [7:0] bram_data;
wire [4:0] bram_cs;
wire bram_wr;

board_cfg_t board_cfg;

always_ff @(posedge clk_ram) begin
    sdr_hs_req <= 0;
    if (sdr_hs_rdy) sdr_hs_ack <= sdr_hs_rq;
    if (sdr_hs_rq != sdr_hs_rq2) begin
        sdr_hs_req <= 1;
        sdr_hs_rq2 <= sdr_hs_rq;
    end
end

//TODO: reset
always_ff @(posedge clk_sys) begin
  hs_mem_read_lat <= hs_read_enable;
  hs_mem_write_lat <= hs_write_enable;
  hs_data_ready <= 0;
  if (!hs_mem_rq_active) begin
    if ((hs_write_enable & ~hs_mem_write_lat) || (hs_read_enable & ~hs_mem_read_lat)) begin
      sdr_hs_wr_sel <= 2'b00;
      sdr_hs_addr <= {REGION_CPU_RAM.base_addr[24:16], hs_address[15:0]};
      if (hs_write_enable) begin
        sdr_hs_wr_sel <= {hs_address[0], ~hs_address[0]};
        sdr_hs_din <= {hs_data_in, hs_data_in};
      end
      sdr_hs_rq <= ~sdr_hs_rq;
      hs_mem_rq_active <= 1;
    end
  end else if (sdr_hs_rq == sdr_hs_ack) begin
    hs_data_out <= hs_address[0] ? sdr_cpu_dout[15:8] : sdr_cpu_dout[7:0];
    hs_mem_rq_active <= 0;
    hs_data_ready <= 1;
  end 
end

sdram sdram
(
    .*,
    .doRefresh(sdr_sprite_refresh),
    .init(~pll_locked),
    .clk(clk_ram),

    .ch1_addr(sdr_bg_addr[24:1]),
    .ch1_dout(sdr_bg_dout),
    .ch1_req(sdr_bg_req),
    .ch1_ready(sdr_bg_rdy),

    .ch2_addr(sdr_sprite_addr[24:1]),
    .ch2_dout(sdr_sprite_dout),
    .ch2_req(sdr_sprite_req),
    .ch2_ready(sdr_sprite_rdy),

    // multiplexed with rom download and cpu read/writes
    .ch3_addr(sdr_ch3_addr[24:1]),
    .ch3_din(sdr_ch3_din),
    .ch3_dout(sdr_cpu_dout),
    .ch3_be(sdr_ch3_be),
    .ch3_rnw(sdr_ch3_rnw),
    .ch3_req(sdr_ch3_req),
    .ch3_ready(sdr_ch3_rdy),

    .ch4_addr(sdr_audio_addr[24:1]),
    .ch4_dout(sdr_audio_dout),
    .ch4_req(sdr_audio_req),
    .ch4_ready(sdr_audio_rdy)
);

rom_loader rom_loader(
    .sys_clk(clk_sys),
    .ram_clk(clk_ram),

    .ioctl_wr(ioctl_wr && !ioctl_index),
    .ioctl_data(ioctl_dout[7:0]),

    .ioctl_wait(ioctl_rom_wait),

    .sdr_addr(sdr_rom_addr),
    .sdr_data(sdr_rom_data),
    .sdr_be(sdr_rom_be),
    .sdr_req(sdr_rom_req),
    .sdr_rdy(sdr_rom_rdy),

    .bram_addr(bram_addr),
    .bram_data(bram_data),
    .bram_cs(bram_cs),
    .bram_wr(bram_wr),

    .board_cfg(board_cfg)
);


// DIP SWITCHES
reg [7:0] dip_sw[8];	// Active-LOW
always @(posedge clk_sys) begin
    if(ioctl_wr && (ioctl_index==254) && !ioctl_addr[24:3])
        dip_sw[ioctl_addr[2:0]] <= ioctl_dout;
end


//////////////////  Arcade Buttons/Interfaces   ///////////////////////////
wire [15:0] keyboard_p1, keyboard_p2, keyboard_p3, keyboard_p4;

wire [15:0] merged_p1 = keyboard_p1 | joystick_p1;
wire [15:0] merged_p2 = keyboard_p2 | joystick_p2;
wire [15:0] merged_p3 = keyboard_p3 | joystick_p3;
wire [15:0] merged_p4 = keyboard_p4 | joystick_p4;

wire [15:0] joystick_combined = joystick_p1 | joystick_p2 | joystick_p3 | joystick_p4;
wire [3:0] key_coin, key_start;
wire key_pause;

mame_keys mame_keys(
    .clk(clk_sys),
    .reset(reset),

    .ps2_key(ps2_key),

    .start(key_start),
    .coin(key_coin),

    .p1(keyboard_p1),
    .p2(keyboard_p2),
    .p3(keyboard_p3),
    .p4(keyboard_p4),

    .pause(key_pause)
);

//Start/coin
wire m_start1   = joystick_p1[10] | key_start[0];
wire m_start2   = joystick_p2[10] | joystick_combined[12] | key_start[1];
wire m_start3   = joystick_p3[10] | key_start[2];
wire m_start4   = joystick_p4[10] | key_start[3];
wire m_coin1    = joystick_combined[11] | |key_coin;
wire m_coin2    = 0;
wire m_pause    = joystick_combined[13] | key_pause;

//////////////////////////////////////////////////////////////////

wire [7:0] R, G, B;
wire HBlank, VBlank, HSync, VSync, hs_core, vs_core;
wire ce_pix;

m92 m92(
    .clk_sys(clk_sys),
    .clk_ram(clk_ram),
    .ce_pix(ce_pix),
    .reset_n(~reset),
    .HBlank(HBlank),
    .VBlank(VBlank),
    .HSync(hs_core),
    .VSync(vs_core),
    .R(R),
    .G(G),
    .B(B),
    .AUDIO_L(AUDIO_L),
    .AUDIO_R(AUDIO_R),

    .board_cfg(board_cfg),

    .coin({2'd0, m_coin2, m_coin1}),
    
    .start_buttons({m_start4, m_start3, m_start2, m_start1}),
    
    .p1_input(merged_p1[9:0]),
    .p2_input(merged_p2[9:0]),
    .p3_input(merged_p3[9:0]),
    .p4_input(merged_p4[9:0]),
   
    .dip_sw({dip_sw[2], dip_sw[1], dip_sw[0]}),

    .sdr_sprite_addr(sdr_sprite_addr),
    .sdr_sprite_dout(sdr_sprite_dout),
    .sdr_sprite_req(sdr_sprite_req),
    .sdr_sprite_rdy(sdr_sprite_rdy),
    .sdr_sprite_refresh(sdr_sprite_refresh),

    .sdr_bg_addr(sdr_bg_addr),
    .sdr_bg_dout(sdr_bg_dout),
    .sdr_bg_req(sdr_bg_req),
    .sdr_bg_rdy(sdr_bg_rdy),

    .sdr_cpu_dout(sdr_cpu_dout),
    .sdr_cpu_din(sdr_cpu_din),
    .sdr_cpu_addr(sdr_cpu_addr),
    .sdr_cpu_req(sdr_cpu_req),
    .sdr_cpu_rdy(sdr_cpu_rdy),
    .sdr_cpu_wr_sel(sdr_cpu_wr_sel),

    .sdr_audio_addr(sdr_audio_addr),
    .sdr_audio_dout(sdr_audio_dout),
    .sdr_audio_req(sdr_audio_req),
    .sdr_audio_rdy(sdr_audio_rdy),

    .clk_bram(clk_sys),
    .bram_addr(bram_addr),
    .bram_data(bram_data),
    .bram_cs(bram_cs),
    .bram_wr(bram_wr),

    .ioctl_download(ioctl_download),
    .ioctl_index(ioctl_index),
	.ioctl_wr(ioctl_wr),
	.ioctl_addr(ioctl_addr),
	.ioctl_dout(ioctl_dout),
	
    .ioctl_upload(ioctl_upload),
    .ioctl_upload_index(ioctl_upload_index),
	.ioctl_din(ioctl_m92_din),
	.ioctl_rd(ioctl_rd),
    .ioctl_upload_req(ioctl_m92_upload_req),

    .pause_rq(system_pause),
    .cpu_paused(cpu_paused),

    .dbg_en_layers(dbg_en_layers),
    .dbg_solid_sprites(dbg_solid_sprites),
    .en_sprites(en_sprites),
    .sprite_freeze(dbg_sprite_freeze),

    .dbg_io_write(ioctl_wr && (ioctl_index == 'd92)),
    .dbg_io_data(ioctl_dout[7:0]),
    .dbg_io_wait(ioctl_dbg_wait)
);

// H/V offset
wire [4:0]	hoffset = status[21:17];
wire [4:0]	voffset = status[26:22];
jtframe_resync #(5) jtframe_resync
(
	.clk(CLK_VIDEO),
	.pxl_cen(ce_pix),
	.hs_in(hs_core),
	.vs_in(vs_core),
	.LVBL(~VBlank),
	.LHBL(~HBlank),
	.hoffset(-hoffset), // flip the sign
	.voffset(-voffset),
	.hs_out(HSync),
	.vs_out(VSync)
);

wire gamma_hsync, gamma_vsync, gamma_hblank, gamma_vblank;
wire [7:0] gamma_r, gamma_g, gamma_b;
gamma_fast video_gamma
(
    .clk_vid(CLK_VIDEO),
    .ce_pix(ce_pix),
    .gamma_bus(gamma_bus),
    .HSync(HSync),
    .VSync(VSync),
    .HBlank(HBlank),
    .VBlank(VBlank),
    .DE(),
    .RGB_in({R, G, B}),
    .HSync_out(gamma_hsync),
    .VSync_out(gamma_vsync),
    .HBlank_out(gamma_hblank),
    .VBlank_out(gamma_vblank),
    .DE_out(),
    .RGB_out({gamma_r, gamma_g, gamma_b})
);

wire VGA_DE_MIXER;
video_mixer #(386, 0, 0) video_mixer(
    .CLK_VIDEO(CLK_VIDEO),
    .CE_PIXEL(CE_PIXEL),
    .ce_pix(ce_pix),

    .scandoubler(forced_scandoubler || scandoubler_fx != 2'b00),
    .hq2x(0),

    .gamma_bus(),

    .R(gamma_r),
    .G(gamma_g),
    .B(gamma_b),

    .HBlank(gamma_hblank),
    .VBlank(gamma_vblank),
    .HSync(gamma_hsync),
    .VSync(gamma_vsync),

    .VGA_R(VGA_R),
    .VGA_G(VGA_G),
    .VGA_B(VGA_B),
    .VGA_VS(VGA_VS),
    .VGA_HS(VGA_HS),
    .VGA_DE(VGA_DE_MIXER),

    .HDMI_FREEZE(HDMI_FREEZE)
);


video_freak video_freak(
    .CLK_VIDEO(CLK_VIDEO),
    .CE_PIXEL(CE_PIXEL),
    .VGA_VS(VGA_VS),
    .HDMI_WIDTH(HDMI_WIDTH),
    .HDMI_HEIGHT(HDMI_HEIGHT),
    .VGA_DE(VGA_DE),
    .VIDEO_ARX(VIDEO_ARX),
    .VIDEO_ARY(VIDEO_ARY),

    .VGA_DE_IN(VGA_DE_MIXER),
    .ARX((!ar) ? ( no_rotate ? 12'd4 : 12'd3 ) : (ar - 1'd1)),
    .ARY((!ar) ? ( no_rotate ? 12'd3 : 12'd4 ) : 12'd0),
    .CROP_SIZE(crop_240p ? 240 : 0),
    .CROP_OFF(crop_offset),
    .SCALE(scale)
);


pause pause(
    .clk_sys(clk_sys),
    .reset(reset),
    .user_button(m_pause),
    .pause_request(hs_pause),
    .options({1'b0, pause_in_osd}),
    .pause_cpu(system_pause),
    .OSD_STATUS(OSD_STATUS)
);

screen_rotate screen_rotate(.*);

//HISCORE

wire [19:0]     hs_address;
wire [7:0]      hs_data_in;
wire [7:0]      hs_data_out;
wire hs_write_enable;
wire hs_read_enable;
wire hs_access_read;
wire hs_access_write;
wire hs_pause;
wire hs_configured;
reg hs_data_ready;
wire cpu_paused;


hiscore #(
                .HS_ADDRESSWIDTH(20),
                .CFG_LENGTHWIDTH(2)
) hi (
        .*,
        .ioctl_upload_req(ioctl_hs_upload_req),
        .clk(clk_sys),
        .paused(cpu_paused),
        .autosave(status[8]),
        .ram_address(hs_address),
        .v_sync(vs_core),
        .data_ready(hs_data_ready),
        .data_from_ram(hs_data_out),
        .data_to_ram(hs_data_in),
        .data_from_hps(ioctl_dout),
        .data_to_hps(ioctl_hs_din),
        .ram_write(hs_write_enable),
        .ram_read(hs_read_enable),
        .ram_intent_read(hs_access_read),
        .ram_intent_write(hs_access_write),
        .pause_cpu(hs_pause),
        .configured(hs_configured)
);
endmodule
