wickerwaka/Arcade-IremM92_MiSTer/rtl/ga23.sv

//============================================================================
//  Copyright (C) 2023 Martin Donlon
//
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
module GA23(
    input clk,
    input clk_ram,

    input ce,

    input paused,

    input reset,

    input mem_cs,
    input mem_wr,
    input mem_rd,
    input io_wr,

    output busy,

    input [15:0] addr,
    input [15:0] cpu_din,
    output reg [15:0] cpu_dout,
    
    output reg [14:0] vram_addr,
    input [15:0] vram_din,
    output reg [15:0] vram_dout,
    output reg vram_we,

    input large_tileset,

    input [63:0] sdr_data,
    output [24:0] sdr_addr,
    output sdr_req,
    input sdr_rdy,

    output vblank,
    output vsync,
    output hblank,
    output hsync,

    output hpulse,
    output vpulse,

    output hint,

    output reg [10:0] color_out,
    output reg prio_out,

    input [2:0] dbg_en_layers
);


//// VIDEO TIMING
reg [9:0] hcnt, vcnt;
reg [9:0] hint_line;

assign hsync = hcnt < 10'd71 || hcnt > 10'd454;
assign hblank = hcnt < 10'd104 || hcnt > 10'd422;
assign vblank = vcnt > 10'd113 && vcnt < 10'd136;
assign vsync = vcnt > 10'd119 && vcnt < 10'd125;
assign hpulse = hcnt == 10'd48;
assign vpulse = (vcnt == 10'd124 && hcnt > 10'd260) || (vcnt == 10'd125 && hcnt < 10'd260);
assign hint = vcnt == hint_line && hcnt > 10'd422 && ~paused;

always_ff @(posedge clk) begin
    if (ce) begin
        hcnt <= hcnt + 10'd1;
        if (hcnt == 10'd471) begin
            hcnt <= 10'd48;
            vcnt <= vcnt + 10'd1;
            if (vcnt == 10'd375) begin
                vcnt <= 10'd114;
            end
        end
    end
end

wire [21:0] rom_addr[3];
wire [31:0] rom_data[3];
wire        rom_req[3];
wire        rom_rdy[3];

ga23_sdram sdram(
    .clk(clk),
    .clk_ram(clk_ram),

    .addr_a(rom_addr[0]),
    .data_a(rom_data[0]),
    .req_a(rom_req[0]),
    .rdy_a(rom_rdy[0]),

    .addr_b(rom_addr[1]),
    .data_b(rom_data[1]),
    .req_b(rom_req[1]),
    .rdy_b(rom_rdy[1]),

    .addr_c(rom_addr[2]),
    .data_c(rom_data[2]),
    .req_c(rom_req[2]),
    .rdy_c(rom_rdy[2]),

    .sdr_addr(sdr_addr),
    .sdr_data(sdr_data),
    .sdr_req(sdr_req),
    .sdr_rdy(sdr_rdy)
);

//// MEMORY ACCESS
reg [2:0] mem_cyc;
reg [3:0] rs_cyc;
reg busy_we;

reg [9:0] x_ofs[3], y_ofs[3];
reg [7:0] control[3];
reg [9:0] rowscroll[3];

wire [14:0] layer_vram_addr[3];
reg layer_load[3];
wire layer_prio[3];
wire [10:0] layer_color[3];
reg [15:0] vram_latch;

reg [1:0] cpu_access_st;
reg cpu_access_we;

reg [37:0] control_save_0[512];
reg [37:0] control_save_1[512];
reg [37:0] control_save_2[512];

reg [37:0] control_restore[3];

reg rowscroll_active, rowscroll_pending;

assign busy = |cpu_access_st;

always_ff @(posedge clk) begin
    bit [9:0] rs_y;
    if (reset) begin
        mem_cyc <= 0;
        cpu_access_st <= 2'd0;
        vram_we <= 0;
        
        // layer regs
        x_ofs[0] <= 10'd0; x_ofs[1] <= 10'd0; x_ofs[2] <= 10'd0;
        y_ofs[0] <= 10'd0; y_ofs[1] <= 10'd0; y_ofs[2] <= 10'd0;
        control[0] <= 8'd0; control[1] <= 8'd0; control[2] <= 8'd0;
        hint_line <= 10'd0;

        rowscroll_pending <= 0;
        rowscroll_active <= 0;

    end else begin
        if (mem_cs & (mem_rd | mem_wr)) begin
            cpu_access_st <= 2'd1;
            cpu_access_we <= mem_wr;
        end
        
        vram_we <= 0;

        if (ce) begin
            layer_load[0] <= 0; layer_load[1] <= 0; layer_load[2] <= 0;
            mem_cyc <= mem_cyc + 3'd1;

            if (hpulse) begin
                mem_cyc <= 3'd7;
                rowscroll_pending <= 1;
            end

            if (rowscroll_active) begin
                rs_cyc <= rs_cyc + 4'd1;
                case(rs_cyc)
                0: vram_addr <= 'h7800;
                4: begin
                    rs_y = y_ofs[0] + vcnt;
                    vram_addr <= 'h7a00 + rs_y[8:0];
                end
                7: rowscroll[0] <= vram_din[9:0];
                8: begin
                    rs_y = y_ofs[1] + vcnt;
                    vram_addr <= 'h7c00 + rs_y[8:0];
                end
                10: rowscroll[1] <= vram_din[9:0];
                12: begin
                    rs_y = y_ofs[2] + vcnt;
                    vram_addr <= 'h7e00 + rs_y[8:0];
                end
                14: rowscroll[2] <= vram_din[9:0];
                15: rowscroll_active <= 0;
                endcase
                
            end else begin

                case(mem_cyc)
                3'd0: begin
                    vram_addr <= layer_vram_addr[0];
                end
                3'd1: begin
                    vram_addr[0] <= 1;
                    vram_latch <= vram_din;
                    layer_load[0] <= 1;
                end
                3'd2: begin
                    vram_addr <= layer_vram_addr[1];
                end
                3'd3: begin
                    vram_addr[0] <= 1;
                    vram_latch <= vram_din;
                    layer_load[1] <= 1;
                end
                3'd4: begin
                    vram_addr <= layer_vram_addr[2];
                end
                3'd5: begin
                    vram_addr[0] <= 1;
                    vram_latch <= vram_din;
                    layer_load[2] <= 1;
                end
                3'd6: begin
                    if (cpu_access_st == 2'd1) begin
                        vram_addr <= addr[15:1];
                        vram_we <= cpu_access_we;
                        vram_dout <= cpu_din;
                        cpu_access_st <= 2'd2;
                    end
                end
                3'd7: begin
                    if (cpu_access_st == 2'd2) begin
                        cpu_access_st <= 2'd0;
                        cpu_access_we <= 0;
                        cpu_dout <= vram_din;
                    end

                    if (rowscroll_pending) begin
                        rowscroll_pending <= 0;
                        rowscroll_active <= 1;
                        rs_cyc <= 4'd0;
                    end
                end
                endcase
            end

            prio_out <= layer_prio[0] | layer_prio[1] | layer_prio[2];
            if (|layer_color[0][3:0]) begin
                color_out <= layer_color[0];
            end else if (|layer_color[1][3:0]) begin
                color_out <= layer_color[1];
            end else begin
                color_out <= layer_color[2];
            end
        end

        if (io_wr) begin
            case(addr[7:0])
            'h80: y_ofs[0][7:0] <= cpu_din[7:0];
            'h81: y_ofs[0][9:8] <= cpu_din[1:0];
            'h84: x_ofs[0][7:0] <= cpu_din[7:0];
            'h85: x_ofs[0][9:8] <= cpu_din[1:0];
            
            'h88: y_ofs[1][7:0] <= cpu_din[7:0];
            'h89: y_ofs[1][9:8] <= cpu_din[1:0];
            'h8c: x_ofs[1][7:0] <= cpu_din[7:0];
            'h8d: x_ofs[1][9:8] <= cpu_din[1:0];
            
            'h90: y_ofs[2][7:0] <= cpu_din[7:0];
            'h91: y_ofs[2][9:8] <= cpu_din[1:0];
            'h94: x_ofs[2][7:0] <= cpu_din[7:0];
            'h95: x_ofs[2][9:8] <= cpu_din[1:0];

            'h98: control[0] <= cpu_din[7:0];
            'h9a: control[1] <= cpu_din[7:0];
            'h9c: control[2] <= cpu_din[7:0];

            'h9e: hint_line[7:0] <= cpu_din[7:0];
            'h9f: hint_line[9:8] <= cpu_din[1:0];
            endcase
        end

        if (hcnt == 10'd104 && ~paused) begin // end of hblank
            control_save_0[vcnt] <= { y_ofs[0], x_ofs[0], control[0], rowscroll[0] };
            control_save_1[vcnt] <= { y_ofs[1], x_ofs[1], control[1], rowscroll[1] };
            control_save_2[vcnt] <= { y_ofs[2], x_ofs[2], control[2], rowscroll[2] };
        end else if (paused) begin
            control_restore[0] <= control_save_0[vcnt];
            control_restore[1] <= control_save_1[vcnt];
            control_restore[2] <= control_save_2[vcnt];
        end
    end
end



//// LAYERS
generate
	genvar i;
    for(i = 0; i < 3; i = i + 1 ) begin : generate_layer
        wire [9:0] _y_ofs = paused ? control_restore[i][37:28] : y_ofs[i];
        wire [9:0] _x_ofs = paused ? control_restore[i][27:18] : x_ofs[i];
        wire [7:0] _control = paused ? control_restore[i][17:10] : control[i];
        wire [9:0] _rowscroll = paused ? control_restore[i][9:0] : rowscroll[i];

        ga23_layer layer(
            .clk(clk),
            .ce_pix(ce),

            .NL(0),
            .large_tileset(large_tileset),

            .x_ofs(_x_ofs),
            .y_ofs(_y_ofs),
            .control(_control),

            .x_base({hcnt[9:3], 3'd0}),
            .y(_y_ofs + vcnt),
            .rowscroll(_rowscroll),

            .vram_addr(layer_vram_addr[i]),

            .load(layer_load[i]),
            .attrib(vram_din),
            .index(vram_latch),

            .color_out(layer_color[i]),
            .prio_out(layer_prio[i]),

            .sdr_addr(rom_addr[i]),
            .sdr_data(rom_data[i]),
            .sdr_req(rom_req[i]),
            .sdr_rdy(rom_rdy[i]),

            .dbg_enabled(dbg_en_layers[i])
        );
    end
endgenerate
endmodule
