wickerwaka/Arcade-IremM92_MiSTer/rtl/ga23_sdram.sv

//============================================================================
//  Copyright (C) 2023 Martin Donlon
//
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
import m92_pkg::*;

module ga23_sdram(
    input clk,
    input clk_ram,

    input [21:0] addr_a,
    output reg [31:0] data_a,
    input req_a,
    output reg rdy_a,

    input [21:0] addr_b,
    output reg [31:0] data_b,
    input req_b,
    output reg rdy_b,

    input [21:0] addr_c,
    output reg [31:0] data_c,
    input req_c,
    output reg rdy_c,

    output reg [24:0] sdr_addr,
    input [31:0] sdr_data,
    output reg sdr_req,
    input sdr_rdy
);

reg [1:0] active = 0;

reg active_rq = 0;
reg active_ack = 0;
reg [31:0] active_data;

reg req_a_2 = 0;
reg req_b_2 = 0;
reg req_c_2 = 0;
reg [24:0] addr_a_2, addr_b_2, addr_c_2;

always @(posedge clk) begin
    sdr_req <= 0;
    rdy_a <= 0;
    rdy_b <= 0;
    rdy_c <= 0;

    if (req_a & ~req_a_2) begin
        req_a_2 <= 1;
        addr_a_2 <= REGION_TILE.base_addr[24:0] | addr_a;
    end

    if (req_b & ~req_b_2) begin
        req_b_2 <= 1;
        addr_b_2 <= REGION_TILE.base_addr[24:0] | addr_b;
    end

    if (req_c & ~req_c_2) begin
        req_c_2 <= 1;
        addr_c_2 <= REGION_TILE.base_addr[24:0] | addr_c;
    end

    if (active) begin
        if (active_ack == active_rq) begin
            active <= 0;
            if (active == 2'd1) begin
                data_a <= active_data;
                rdy_a <= 1;
            end

            if (active == 2'd2) begin
                data_b <= active_data;
                rdy_b <= 1;
            end

            if (active == 2'd3) begin
                data_c <= active_data;
                rdy_c <= 1;
            end
        end
    end else begin
        if (req_a_2) begin
            sdr_addr <= addr_a_2;
            sdr_req <= 1;
            active_rq <= ~active_rq;
            active <= 2'd1;
            req_a_2 <= 0;
        end else if (req_b_2) begin
            sdr_addr <= addr_b_2;
            sdr_req <= 1;
            active_rq <= ~active_rq;
            active <= 2'd2;
            req_b_2 <= 0;
        end else if (req_c_2) begin
            sdr_addr <= addr_c_2;
            sdr_req <= 1;
            active_rq <= ~active_rq;
            active <= 2'd3;
            req_c_2 <= 0;
        end
    end
end

always @(posedge clk_ram) begin
    if (sdr_rdy) begin
        active_ack <= active_rq;
        active_data <= sdr_data;
    end
end

endmodule
