wickerwaka/Arcade-IremM92_MiSTer/rtl/rom.sv

//============================================================================
//  Irem M92 for MiSTer FPGA - ROM loading
//
//  Copyright (C) 2023 Martin Donlon
//
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
import m92_pkg::*;

module rom_loader
(
    input sys_clk,
    input ram_clk,

    input ioctl_wr,
    input [7:0] ioctl_data,

    output ioctl_wait,

    output [24:0] sdr_addr,
    output [15:0] sdr_data,
    output [1:0] sdr_be,
    output sdr_req,
    input sdr_rdy,

    output [19:0] bram_addr,
    output [7:0] bram_data,
    output reg [4:0] bram_cs,
    output bram_wr,

    output board_cfg_t board_cfg
);

reg [24:0] base_addr;
reg reorder_64;
reg [24:0] offset;
reg [23:0] size;

enum {
    BOARD_CFG,
    REGION_IDX,
    SIZE_0,
    SIZE_1,
    SIZE_2,
    SDR_DATA,
    BRAM_DATA
} stage = BOARD_CFG;

reg [3:0] region = 0;

reg write_rq = 0;
reg write_ack = 0;

always @(posedge sys_clk) begin
    if (write_ack == write_rq) begin
        sdr_req <= 0;
        ioctl_wait <= 0;
    end

    bram_wr <= 0;
    
    if (ioctl_wr) begin
        case (stage)
        BOARD_CFG: begin board_cfg <= board_cfg_t'(ioctl_data); stage <= REGION_IDX; end
        REGION_IDX: begin
            if (ioctl_data == 8'hff) region <= region + 4'd1;
            else region <= ioctl_data[3:0];
            stage <= SIZE_0;
        end
        SIZE_0: begin size[23:16] <= ioctl_data; stage <= SIZE_1; end
        SIZE_1: begin size[15:8] <= ioctl_data; stage <= SIZE_2; end
        SIZE_2: begin
            size[7:0] <= ioctl_data;
            base_addr <= LOAD_REGIONS[region].base_addr;
            reorder_64 <= LOAD_REGIONS[region].reorder_64;
            bram_cs <= LOAD_REGIONS[region].bram_cs;
            offset <= 25'd0;

            if ({size[23:8], ioctl_data} == 24'd0)
                stage <= REGION_IDX;
            else if (LOAD_REGIONS[region].bram_cs != 0)
                stage <= BRAM_DATA;
            else
                stage <= SDR_DATA;
        end
        SDR_DATA: begin
            if (reorder_64)
                sdr_addr <= base_addr[24:0] + {offset[24:7], offset[5:2], offset[6], offset[1:0]};
            else
                sdr_addr <= base_addr[24:0] + offset[24:0];
            sdr_data = {ioctl_data, ioctl_data};
            sdr_be <= { offset[0], ~offset[0] };
            offset <= offset + 25'd1;
            sdr_req <= 1;
            ioctl_wait <= 1;
            write_rq <= ~write_rq; 

            if (offset == ( size - 1)) stage <= REGION_IDX;
        end
        BRAM_DATA: begin
            bram_addr <= offset[19:0];
            bram_data <= ioctl_data;
            bram_wr <= 1;
            offset <= offset + 25'd1;

            if (offset == ( size - 1)) stage <= REGION_IDX;
        end
        endcase
    end
end

always @(posedge ram_clk) begin
    if (sdr_rdy) begin
        write_ack <= write_rq;
    end
end

endmodule
